MaterialFoundry/MaterialPlane/docs/index.md

# Material Plane Documentation

Welcome to the Material Plane documentation.

Click the links below or at the top of the page to navigate the documentation:

* [Production Hardware](Production/gettingStarted.md)
* [DIY Hardware](DIY/gettingStarted.md)
* [Touch](Touch/gettingStarted.md)
* [Display Considerations](DisplayConsiderations/type.md)
* [Hardware Comparison](hardwareComparison.md)
* [FAQ](faq.md)

## Introduction
Material Plane is a <a href="https://foundryvtt.com/">Foundry VTT</a> module that allows physical minis to be tracked by Foundry when using a horizontally mounted TV. This allows you to bring the joy of physical minis into Foundry.<br>
<br>
There are currently 2 ways to track minis:<br>

### Material Plane sensor
The system consists of an IR sensor, and IR enabled mini bases. These bases contain IR LEDs that are tracked by the sensor. The sensor then relays this information to foundry over WiFi, where the information is interpreted as token movement.<br>
You can use any TV, monitor or projector for this.<br>
There is a pre-assembled and advanced version of the hardware for sale on the [Material Foundry webshop](https://www.materialfoundry.nl/), or it is possible to build DIY hardware.

### Touch Screen
There is currently experimental support for touch screen devices. Either capacitive touch screens or normal TVs with an IR touch frame can work.<br>
<br>
Please take a look at [this](hardwareComparison.md) page for a comparison between the Material Plane sensor and touch screen.<br>

## Trailer
<a href="https://www.youtube.com/watch?v=VVTjNrCfUwM">
trailer
</a>

## Important Links

* [Issues/Feature requests](https://github.com/MaterialFoundry/MaterialPlane/issues)
* [Main repository](https://github.com/materialfoundry/materialplane)
* [Foundry module](https://github.com/MaterialFoundry/MaterialPlane_Foundry) ([Releases](https://github.com/MaterialFoundry/MaterialPlane_Foundry/releases))
* [Sensor firmware](https://github.com/MaterialFoundry/MaterialPlane_Sensor) ([Releases](https://github.com/MaterialFoundry/MaterialPlane_Sensor/releases))
* [Base firmware](https://github.com/MaterialFoundry/MaterialPlane_Base) ([Releases](https://github.com/MaterialFoundry/MaterialPlane_Base/releases))
* [Pen firmware](https://github.com/MaterialFoundry/MaterialPlane_Pen) ([Releases](https://github.com/MaterialFoundry/MaterialPlane_Pen/releases))
* [Material Companion](https://github.com/MaterialFoundry/MaterialCompanion) ([Releases](https://github.com/MaterialFoundry/MaterialCompanion/releases))
* [Arduino core](https://github.com/MaterialFoundry/MaterialFoundry_Arduino) ([Releases](https://github.com/MaterialFoundry/MaterialFoundry_Arduino/releases))
* [3D models](https://github.com/MaterialFoundry/MaterialPlane_Models)
* [Discord server](https://discord.gg/3hd4G6TkmA)
* [Patreon](https://www.patreon.com/materialfoundry)

## Software Versions & Module Incompatibilities
<b>Foundry VTT:</b> v10 & v11<br>
<b>Module Incompatibilities:</b> When moving tokens, Foundry's click and drag system is bypassed. So modules that depend on that functionality might not work.

## Feedback
If you have any suggestions or bugs to report, feel free to contact me on Discord (Cris#6864), or send me an email: info@materialfoundry.nl.

## Credits
<b>Author:</b> Cristian Deenen (Cris#6864 on Discord)<br>
<br>
Please consider supporting me on <a href="https://www.patreon.com/materialfoundry">Patreon</a>, and feel free to join the Material Foundry <a href="https://discord.gg/3hd4G6TkmA">Discord</a> server.
