MaterialFoundry/MaterialPlane/include/diyDisclaimer.md

<div class="warning" style='background-color:#ab4a00; border-radius: 4px; padding:0.7em; color:black; text-align: center;'>
<span>
<p style='margin-top:1em; text-align:center'>
<b>Disclaimer</b></p>
<p style='margin-left:1em;'>
For the DIY hardware you will, as the name suggest, have do it yourself. This includes sourcing parts, basic soldering, and 3D printing. You will be responsible for all troubleshooting.<br><br>
It is your own responsibility to properly build and use the hardware.
Material Foundry cannot be held responsible for any damage, either directly or indirectly caused by Material Foundry or any associated hardware, software or service.
This includes damage caused by incorrect documentation, bugs in the software or firmware, or wrong advise.<br>
<br>
If you are uncomfortable with this, consider buying the <a href="https://www.materialfoundry.nl/" style='color: #000f99'>pre-build production hardware</a>.
</p>
</div>
