MaterialFoundry/MaterialPlane/include/foundryConfig-downloads.md

## Downloads

In the 'Downloads' tab you can download the various firmwares for the Material Plane hardware, and Material Companion.

For each component, you can see the current version, the minimum version (that works with this version of the module), and the latest version.

Select the desired 'variant' (if applicable) and press the 'Download' button to download the file.
