MaterialFoundry/MaterialPlane/docs/DIY/Foundry/foundryConfig.md

{%set variant = 'diy' %}

{% include 'foundryConfig-general.md' %}

{% include 'foundryConfig-sensor.md' %}

{% include 'foundryConfig-downloads.md' %}
