MaterialFoundry/MaterialPlane/docs/DIY/SensorConfiguration/webserver.md

{%set variant = 'diy' %}

{% include 'sensorWebserver.md' %}
