MaterialFoundry/MaterialPlane/docs/DIY/SensorPositioning/sensorOrientation.md

{% set variant = 'diy' %}

{% include 'sensorOrientation.md' %}
