MaterialFoundry/MaterialPlane/docs/DIY/Updating/sensorUpdating.md

{%set variant = 'diy' %}

{% include 'sensorUpdating.md' %}
