MaterialFoundry/MaterialPlane/docs/DIY/SensorConfiguration/sensorSettings.md

{%set variant = 'production' %}

{% include 'sensorSettings.md' %}
