MaterialFoundry/MaterialPlane/docs/Production/Updating/sensorUpdating.md

{%set variant = 'production' %}

{% include 'sensorUpdating.md' %}
