MaterialFoundry/MaterialPlane/docs/Production/SensorPositioning/sensorDistance.md

{% set variant = 'production' %}
{% set lensLink = '../SensorConfiguration/sensorLens.md' %}

{% include 'requirements-displaySensorDistance.md' %}
