MaterialFoundry/MaterialPlane/docs/Production/SensorPositioning/sensorOrientation.md

{% set variant = 'production' %}
{% set lensLink = '../SensorConfiguration/sensorLens.md' %}

{% include 'sensorOrientation.md' %}
