MaterialFoundry/MaterialPlane/docs/img/foundry/.thumb/Foundry_Cal_Multi_Progress.png.jpg

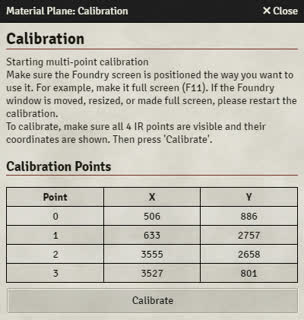
docs/img/foundry/.thumb/Foundry_Cal_Multi_Progress.png.jpg
