MaterialFoundry/MaterialPlane/docs/img/foundry/.thumb/Foundry_Module_Connection.png.jpg

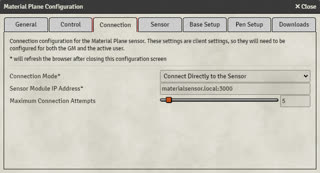
docs/img/foundry/.thumb/Foundry_Module_Connection.png.jpg
