MaterialFoundry/MaterialPlane/docs/img/foundry/.thumb/Foundry_Module_Control.png.jpg

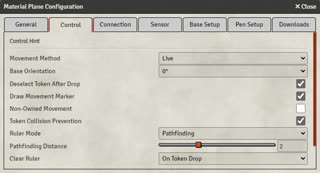
docs/img/foundry/.thumb/Foundry_Module_Control.png.jpg
