MaterialFoundry/MaterialPlane/docs/img/foundry/.thumb/Foundry_Module_Download.png.jpg

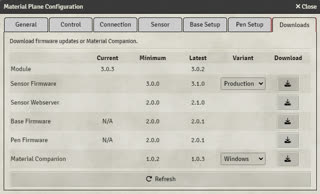
docs/img/foundry/.thumb/Foundry_Module_Download.png.jpg
