MaterialFoundry/MaterialPlane/docs/img/foundry/.thumb/Foundry_Module_Enable.png.jpg

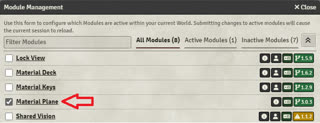
docs/img/foundry/.thumb/Foundry_Module_Enable.png.jpg
