MaterialFoundry/MaterialPlane/docs/img/foundry/.thumb/Foundry_Module_General_Touch.png.jpg

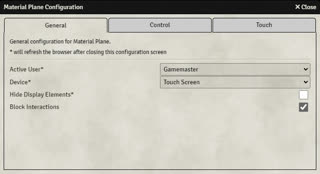
docs/img/foundry/.thumb/Foundry_Module_General_Touch.png.jpg
