MaterialFoundry/MaterialPlane/docs/img/foundry/.thumb/Foundry_Module_Pen.png.jpg

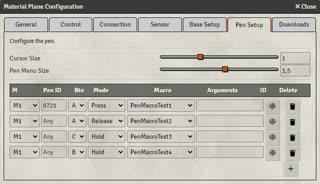
docs/img/foundry/.thumb/Foundry_Module_Pen.png.jpg
