MaterialFoundry/MaterialPlane/docs/img/foundry/.thumb/Foundry_Module_Update_All.png.jpg

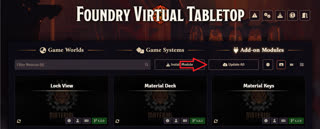
docs/img/foundry/.thumb/Foundry_Module_Update_All.png.jpg
