MaterialFoundry/MaterialPlane/docs/img/foundry/.thumb/Foundry_Module_Update_Single.png.jpg

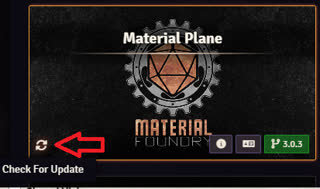
docs/img/foundry/.thumb/Foundry_Module_Update_Single.png.jpg
