MaterialFoundry/MaterialPlane/docs/img/foundry/Foundry_Cal_Single_Progress.png

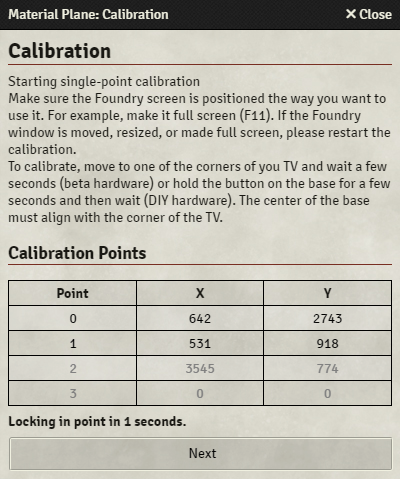
docs/img/foundry/Foundry_Cal_Single_Progress.png
