MaterialFoundry/MaterialPlane/docs/img/foundry/Foundry_Module_Config_Btn.png

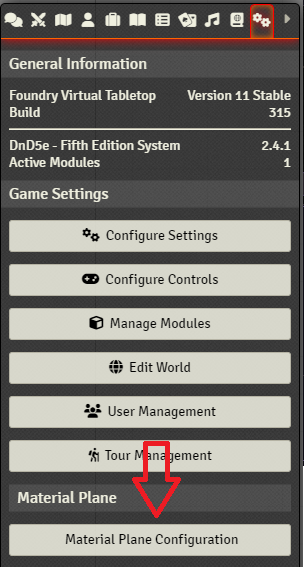
docs/img/foundry/Foundry_Module_Config_Btn.png
