MaterialFoundry/MaterialPlane/docs/img/foundry/Foundry_Module_Download.png

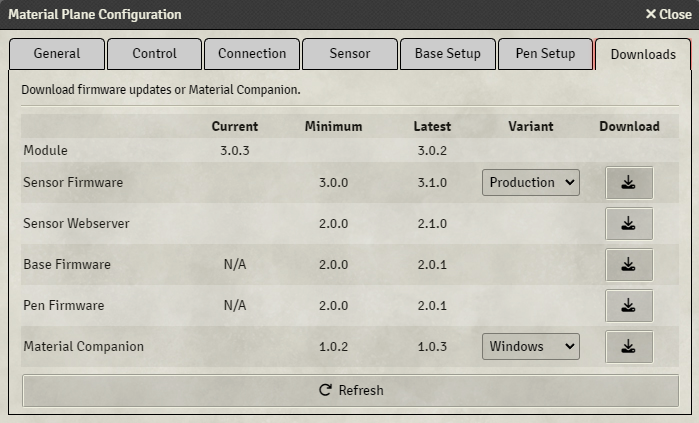
docs/img/foundry/Foundry_Module_Download.png
