MaterialFoundry/MaterialPlane/docs/img/foundry/Foundry_Module_General.png

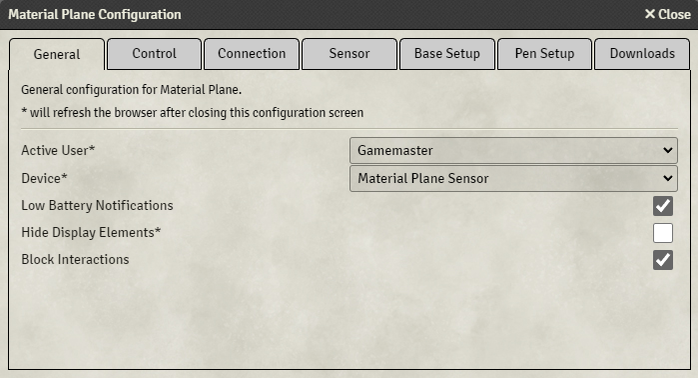
docs/img/foundry/Foundry_Module_General.png
