MaterialFoundry/MaterialPlane/docs/img/hardware/DIY/.thumb/BaseFab.jpg.jpg

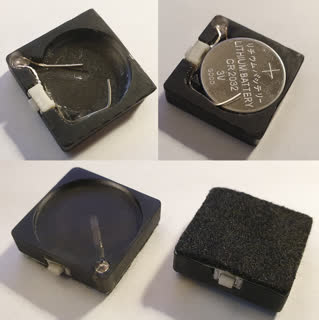
docs/img/hardware/DIY/.thumb/BaseFab.jpg.jpg
