MaterialFoundry/MaterialPlane/docs/img/hardware/DIY/.thumb/DFRobot.jpg.jpg

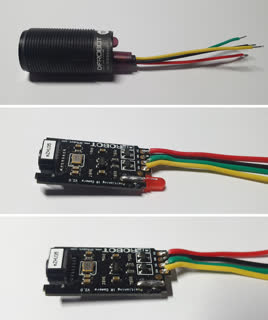
docs/img/hardware/DIY/.thumb/DFRobot.jpg.jpg
