MaterialFoundry/MaterialPlane/docs/img/hardware/DIY/.thumb/Enclosure.jpg.jpg

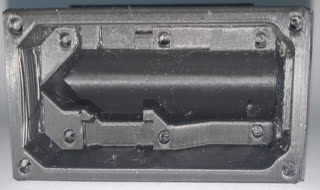
docs/img/hardware/DIY/.thumb/Enclosure.jpg.jpg
