MaterialFoundry/MaterialPlane/docs/img/hardware/DIY/.thumb/GndLead.jpg.jpg

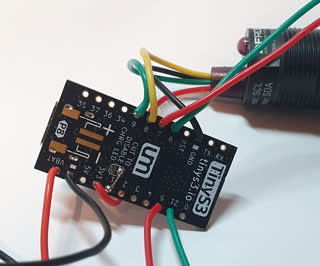
docs/img/hardware/DIY/.thumb/GndLead.jpg.jpg
