MaterialFoundry/MaterialPlane/docs/img/hardware/DIY/.thumb/MiniWithBase.jpg.jpg

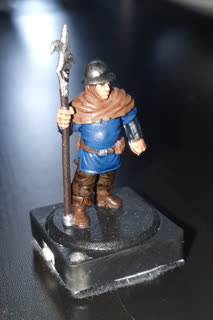
docs/img/hardware/DIY/.thumb/MiniWithBase.jpg.jpg
