MaterialFoundry/MaterialPlane/docs/img/hardware/DIY/.thumb/Sensor.jpg.jpg

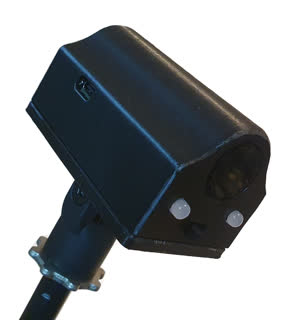
docs/img/hardware/DIY/.thumb/Sensor.jpg.jpg
