MaterialFoundry/MaterialPlane/docs/img/hardware/DIY/.thumb/Switch.jpg.jpg

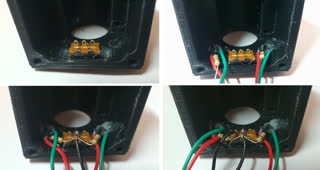
docs/img/hardware/DIY/.thumb/Switch.jpg.jpg
