MaterialFoundry/MaterialPlane/docs/img/hardware/DIY/.thumb/TinyPicoUsbDetect.jpg.jpg

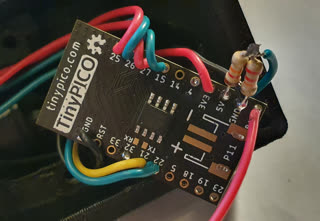
docs/img/hardware/DIY/.thumb/TinyPicoUsbDetect.jpg.jpg
