MaterialFoundry/MaterialPlane/docs/img/hardware/DIY/.thumb/TinyS3UsbDetect.jpg.jpg

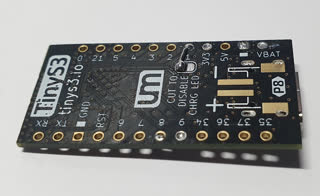
docs/img/hardware/DIY/.thumb/TinyS3UsbDetect.jpg.jpg
