MaterialFoundry/MaterialPlane/docs/img/hardware/production/.thumb/Base_Adapter_Prod.png.jpg

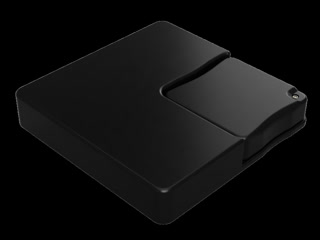
docs/img/hardware/production/.thumb/Base_Adapter_Prod.png.jpg
