MaterialFoundry/MaterialPlane/docs/img/hardware/production/.thumb/Base_Prod.png.jpg

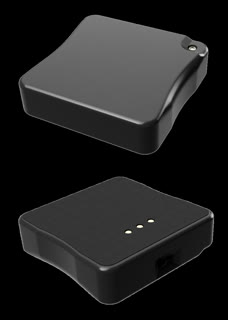
docs/img/hardware/production/.thumb/Base_Prod.png.jpg
