MaterialFoundry/MaterialPlane/docs/img/hardware/production/.thumb/Dock_Charging.png.jpg

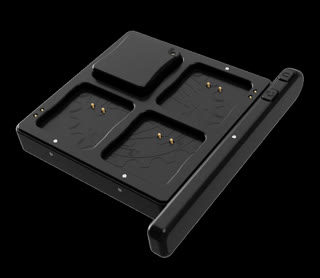
docs/img/hardware/production/.thumb/Dock_Charging.png.jpg
