MaterialFoundry/MaterialPlane/docs/img/hardware/production/.thumb/Dock_Prod.png.jpg

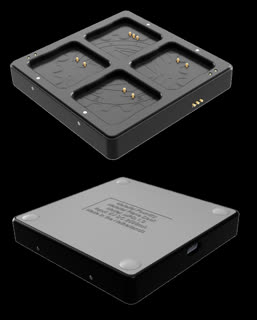
docs/img/hardware/production/.thumb/Dock_Prod.png.jpg
