MaterialFoundry/MaterialPlane/docs/img/hardware/production/.thumb/Expansions_Prod.png.jpg

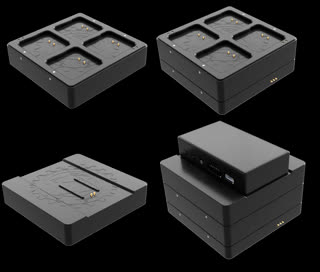
docs/img/hardware/production/.thumb/Expansions_Prod.png.jpg
