MaterialFoundry/MaterialPlane/docs/img/hardware/production/.thumb/Mini_Holding.png.jpg

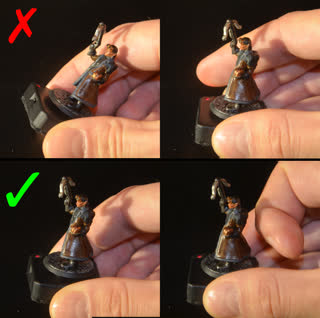
docs/img/hardware/production/.thumb/Mini_Holding.png.jpg
