MaterialFoundry/MaterialPlane/docs/img/hardware/production/.thumb/Mini_Mounting.png.jpg

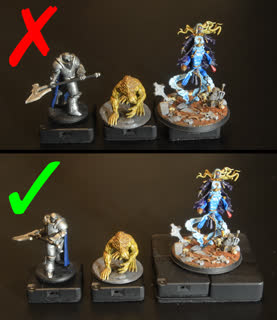
docs/img/hardware/production/.thumb/Mini_Mounting.png.jpg
