MaterialFoundry/MaterialPlane/docs/img/hardware/production/.thumb/Pen_Holding.png.jpg

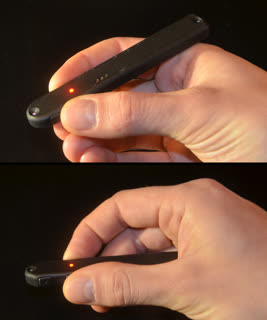
docs/img/hardware/production/.thumb/Pen_Holding.png.jpg
