MaterialFoundry/MaterialPlane/docs/img/hardware/production/.thumb/Pen_Prod.png.jpg

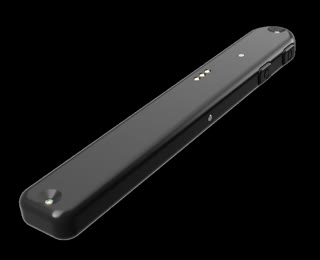
docs/img/hardware/production/.thumb/Pen_Prod.png.jpg
