MaterialFoundry/MaterialPlane/docs/img/hardware/production/.thumb/Sensor_Lens_Removal.png.jpg

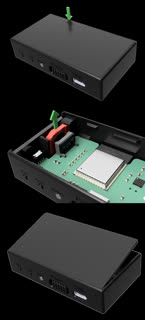
docs/img/hardware/production/.thumb/Sensor_Lens_Removal.png.jpg
