MaterialFoundry/MaterialPlane/docs/img/hardware/production/.thumb/Sensor_Mount.png.jpg

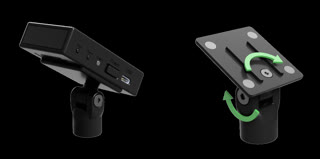
docs/img/hardware/production/.thumb/Sensor_Mount.png.jpg
