MaterialFoundry/MaterialPlane/docs/img/hardware/production/.thumb/Sensor_Mount_Ceiling.png.jpg

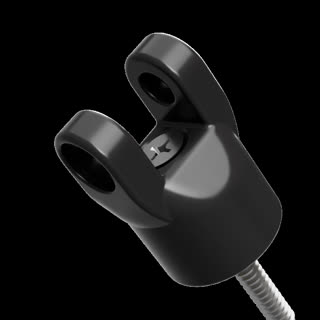
docs/img/hardware/production/.thumb/Sensor_Mount_Ceiling.png.jpg
