MaterialFoundry/MaterialPlane/docs/img/hardware/production/.thumb/Sensor_Prod.png.jpg

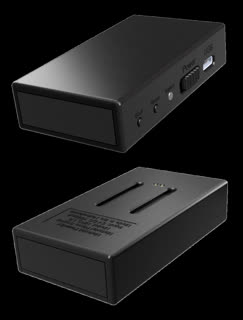
docs/img/hardware/production/.thumb/Sensor_Prod.png.jpg
