MaterialFoundry/MaterialPlane/docs/img/hardware/production/Sensor_Lens_Removal.png

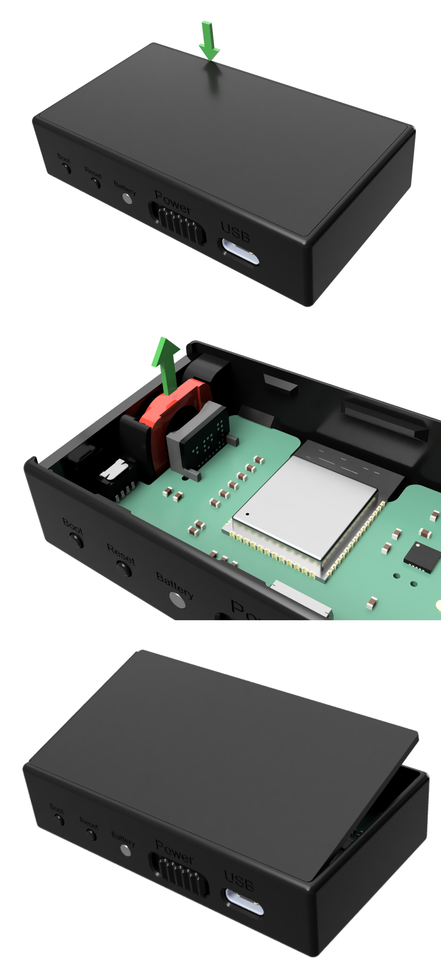
docs/img/hardware/production/Sensor_Lens_Removal.png
