MaterialFoundry/MaterialPlane/docs/img/misc/.thumb/Arduino_Boards.png.jpg

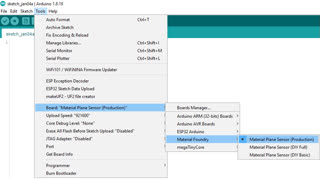
docs/img/misc/.thumb/Arduino_Boards.png.jpg
