MaterialFoundry/MaterialPlane/docs/img/misc/.thumb/Arduino_Port.png.jpg

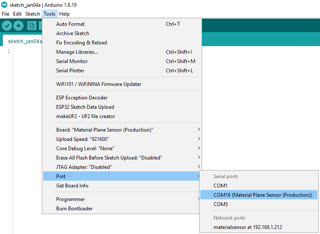
docs/img/misc/.thumb/Arduino_Port.png.jpg
