MaterialFoundry/MaterialPlane/docs/img/misc/.thumb/Arduino_Spiffs.png.jpg

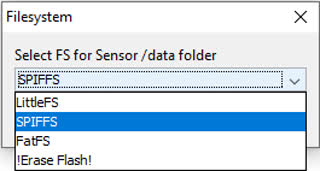
docs/img/misc/.thumb/Arduino_Spiffs.png.jpg
