MaterialFoundry/MaterialPlane/docs/img/misc/.thumb/Arduino_Upload.png.jpg

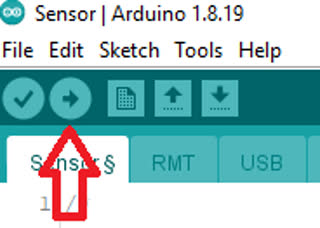
docs/img/misc/.thumb/Arduino_Upload.png.jpg
