MaterialFoundry/MaterialPlane/docs/img/misc/.thumb/Display_Protection.png.jpg

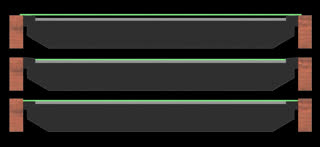
docs/img/misc/.thumb/Display_Protection.png.jpg
