MaterialFoundry/MaterialPlane/docs/img/misc/.thumb/Sensor_Placement_GM_Short.png.jpg

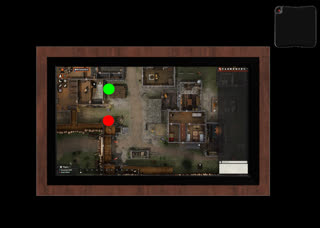
docs/img/misc/.thumb/Sensor_Placement_GM_Short.png.jpg
