MaterialFoundry/MaterialPlane/docs/img/misc/.thumb/SensorPlacement.png.jpg

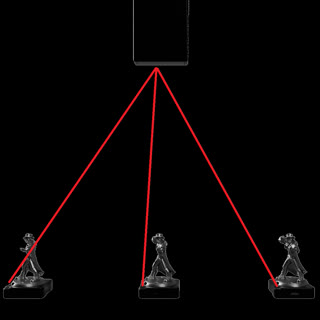
docs/img/misc/.thumb/SensorPlacement.png.jpg
