MaterialFoundry/MaterialPlane/docs/img/misc/.thumb/Serial_Scan_Wifi.png.jpg

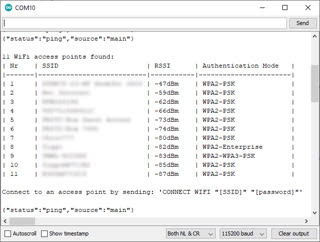
docs/img/misc/.thumb/Serial_Scan_Wifi.png.jpg
