MaterialFoundry/MaterialPlane/docs/img/misc/Arduino_Boards_Manager.png

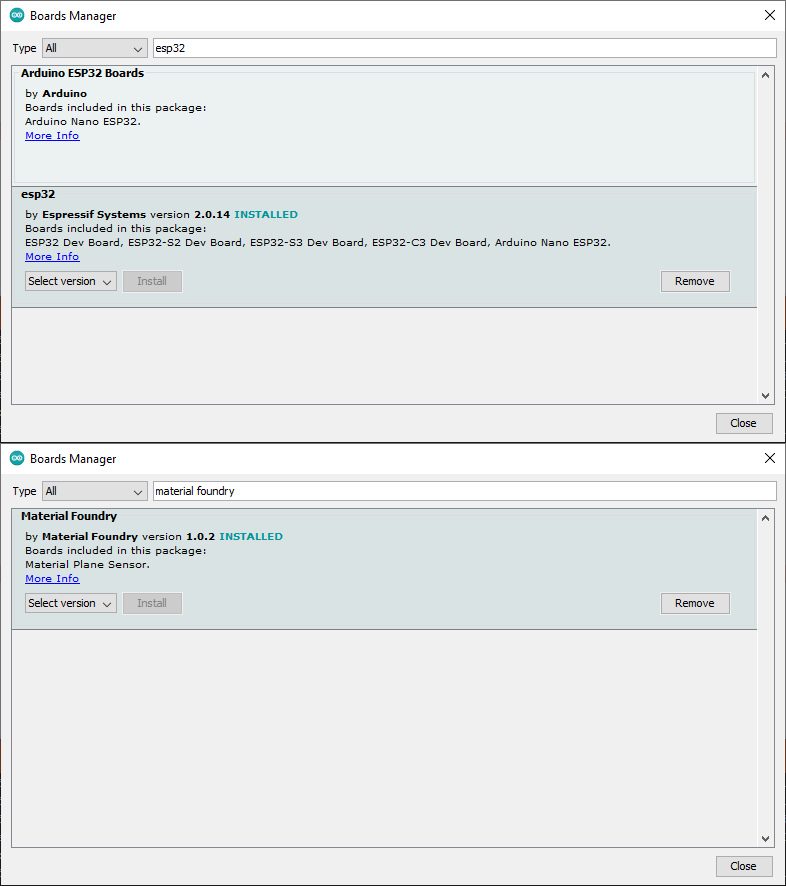
docs/img/misc/Arduino_Boards_Manager.png
