MaterialFoundry/MaterialPlane/docs/img/webserver/.thumb/Webserver_Console.png.jpg

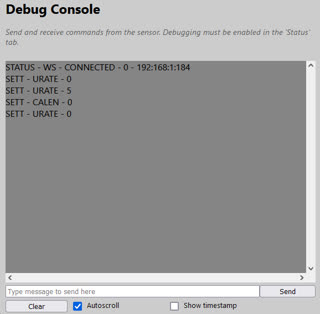
docs/img/webserver/.thumb/Webserver_Console.png.jpg
