MaterialFoundry/MaterialPlane/docs/img/webserver/.thumb/Webserver_Coordinates.png.jpg

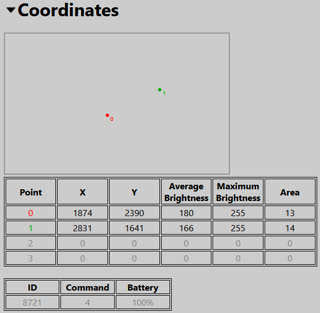
docs/img/webserver/.thumb/Webserver_Coordinates.png.jpg
