MaterialFoundry/MaterialPlane/docs/img/webserver/.thumb/Webserver_Coordinates_DIY.png.jpg

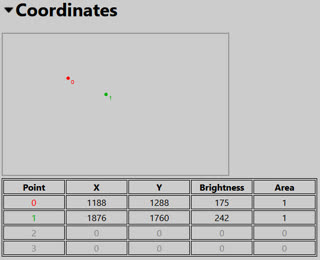
docs/img/webserver/.thumb/Webserver_Coordinates_DIY.png.jpg
