MaterialFoundry/MaterialPlane/docs/img/webserver/.thumb/Webserver_Reset.png.jpg

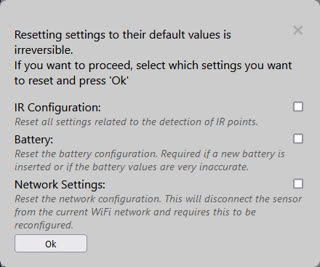
docs/img/webserver/.thumb/Webserver_Reset.png.jpg
