MaterialFoundry/MaterialPlane/docs/img/webserver/.thumb/Webserver_Update.png.jpg

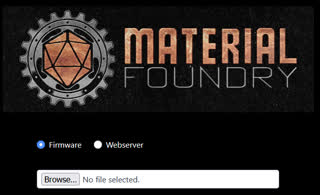
docs/img/webserver/.thumb/Webserver_Update.png.jpg
