MaterialFoundry/MaterialPlane/docs/img/webserver/Webserver_Battery_DIY.png

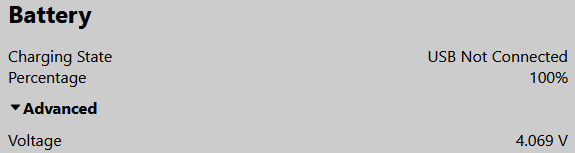
docs/img/webserver/Webserver_Battery_DIY.png
