MaterialFoundry/MaterialPlane/docs/img/webserver/Webserver_Status.png

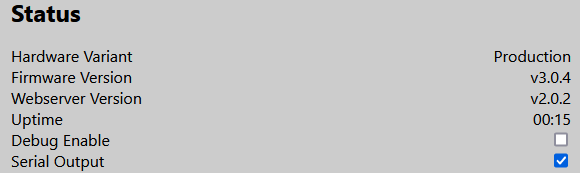
docs/img/webserver/Webserver_Status.png
