MaterialFoundry/MaterialPlane/docs/img/webserver/Webserver_Status_Tab.png

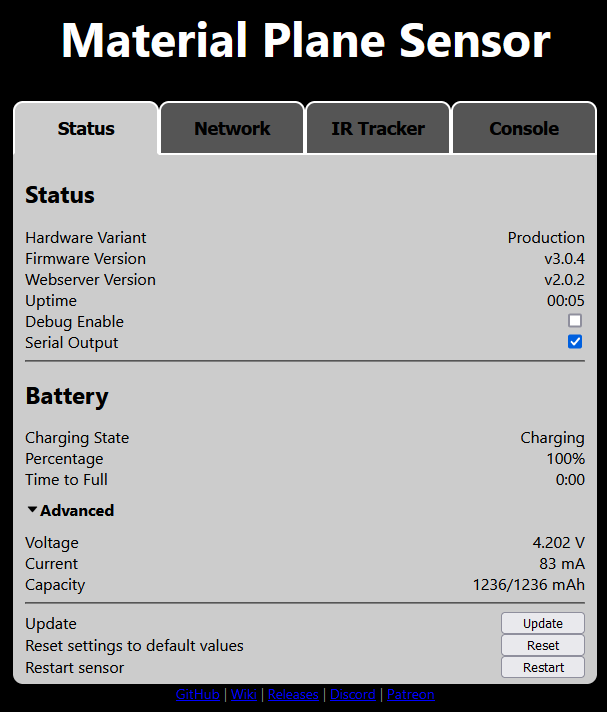
docs/img/webserver/Webserver_Status_Tab.png
