MaterialFoundry/MaterialPlane/Img/Beta Hardware/20210420_232709.jpg

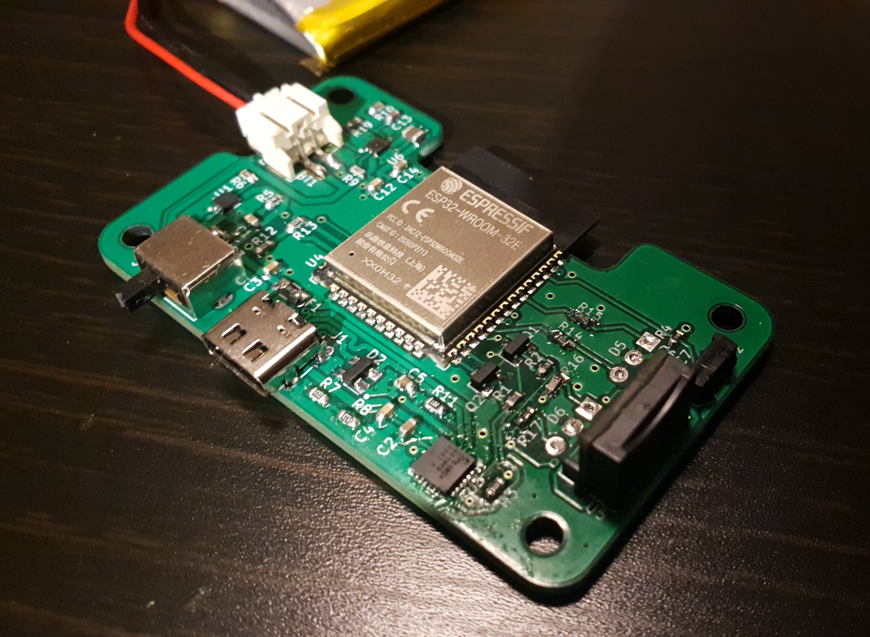
Img/Beta Hardware/20210420_232709.jpg
