MaterialFoundry/MaterialPlane/Img/Beta Hardware/.thumb/Base.jpg.jpg

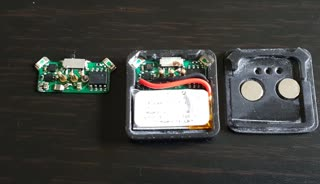
Img/Beta Hardware/.thumb/Base.jpg.jpg
