MaterialFoundry/MaterialPlane/Img/Beta Hardware/.thumb/MP_Base.jpg.jpg

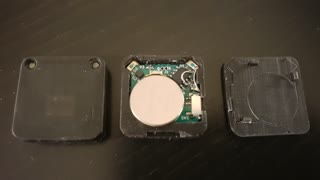
Img/Beta Hardware/.thumb/MP_Base.jpg.jpg
