MaterialFoundry/MaterialPlane/Img/Beta Hardware/.thumb/MP_Dock_ConceptArt.png.jpg

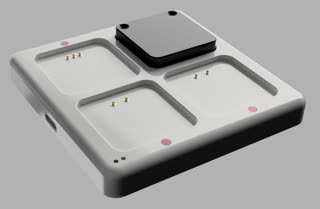
Img/Beta Hardware/.thumb/MP_Dock_ConceptArt.png.jpg
