MaterialFoundry/MaterialPlane/Img/Beta Hardware/.thumb/MP_PCBs.jpg.jpg

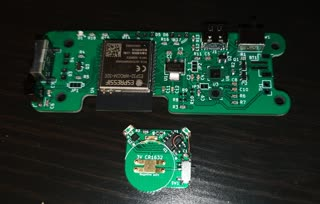
Img/Beta Hardware/.thumb/MP_PCBs.jpg.jpg
