MaterialFoundry/MaterialPlane/Img/Beta Hardware/.thumb/SensorBaseAndDock.jpg.jpg

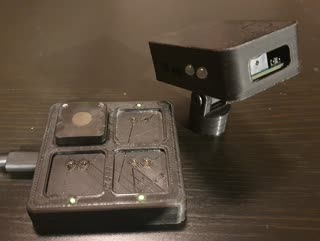
Img/Beta Hardware/.thumb/SensorBaseAndDock.jpg.jpg
