MaterialFoundry/MaterialPlane/Img/DIY Hardware/.thumb/BaseBottom.jpg.jpg

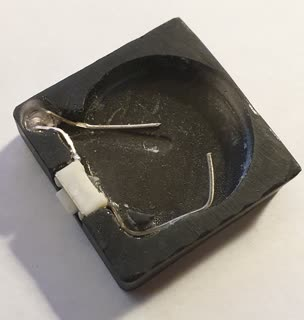
Img/DIY Hardware/.thumb/BaseBottom.jpg.jpg
