MaterialFoundry/MaterialPlane/Img/DIY Hardware/.thumb/BaseBottomBattery.jpg.jpg

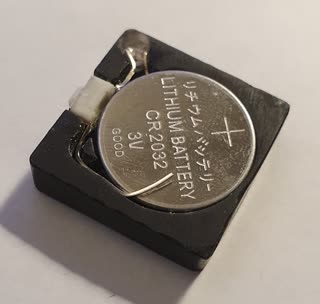
Img/DIY Hardware/.thumb/BaseBottomBattery.jpg.jpg
