MaterialFoundry/MaterialPlane/Img/DIY Hardware/.thumb/Bases.jpg.jpg

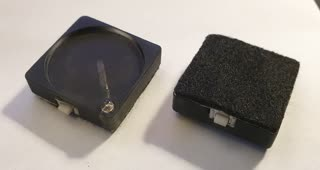
Img/DIY Hardware/.thumb/Bases.jpg.jpg
