MaterialFoundry/MaterialPlane/Img/DIY Hardware/.thumb/Battery.jpg.jpg

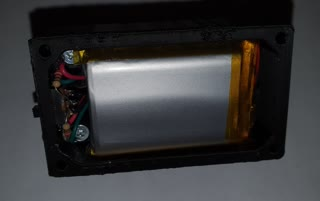
Img/DIY Hardware/.thumb/Battery.jpg.jpg
