MaterialFoundry/MaterialPlane/Img/DIY Hardware/.thumb/Brackets.jpg.jpg

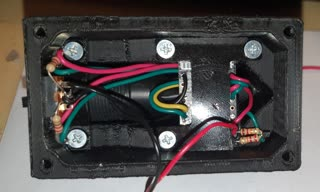
Img/DIY Hardware/.thumb/Brackets.jpg.jpg
