MaterialFoundry/MaterialPlane/Img/DIY Hardware/.thumb/FullSensor.jpg.jpg

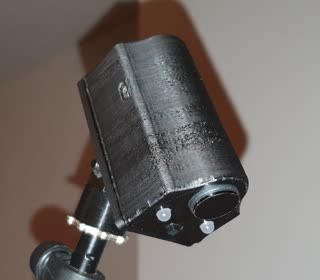
Img/DIY Hardware/.thumb/FullSensor.jpg.jpg
