MaterialFoundry/MaterialPlane/Img/DIY Hardware/.thumb/LEDsNextToSwitch.jpg.jpg

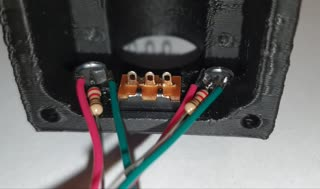
Img/DIY Hardware/.thumb/LEDsNextToSwitch.jpg.jpg
