MaterialFoundry/MaterialPlane/Img/DIY Hardware/.thumb/Lid.jpg.jpg

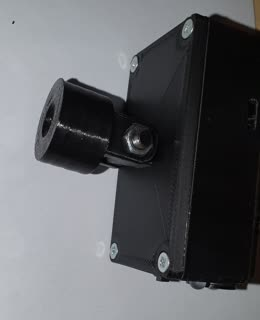
Img/DIY Hardware/.thumb/Lid.jpg.jpg
