MaterialFoundry/MaterialPlane/Img/DIY Hardware/.thumb/RemoveLED1.jpg.jpg

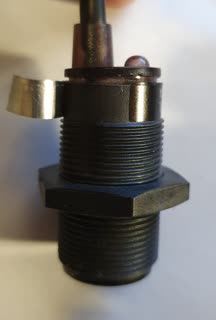
Img/DIY Hardware/.thumb/RemoveLED1.jpg.jpg
