MaterialFoundry/MaterialPlane/Img/DIY Hardware/.thumb/RemoveLED2.jpg.jpg

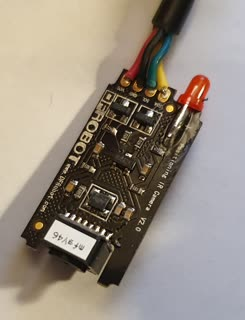
Img/DIY Hardware/.thumb/RemoveLED2.jpg.jpg
