MaterialFoundry/MaterialPlane/Img/DIY Hardware/.thumb/RemoveLED3.jpg.jpg

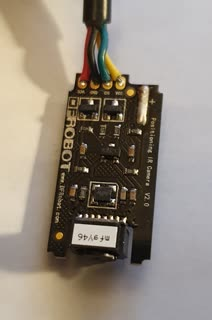
Img/DIY Hardware/.thumb/RemoveLED3.jpg.jpg
