MaterialFoundry/MaterialPlane/Img/DIY Hardware/.thumb/SensorCutWires.jpg.jpg

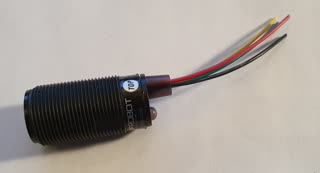
Img/DIY Hardware/.thumb/SensorCutWires.jpg.jpg
