MaterialFoundry/MaterialPlane/Img/DIY Hardware/.thumb/SensorMount.jpg.jpg

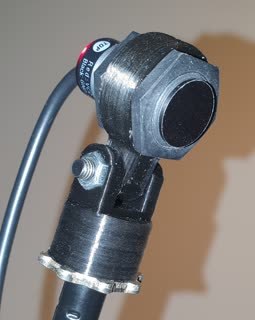
Img/DIY Hardware/.thumb/SensorMount.jpg.jpg
