MaterialFoundry/MaterialPlane/Img/DIY Hardware/.thumb/Switches2.jpg.jpg

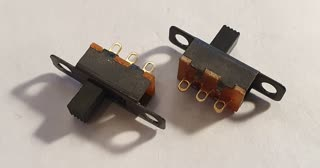
Img/DIY Hardware/.thumb/Switches2.jpg.jpg
