MaterialFoundry/MaterialPlane/Img/DIY Hardware/.thumb/Switches.jpg.jpg

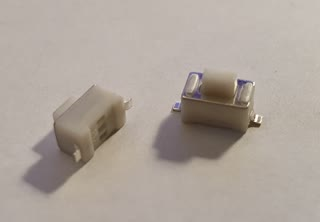
Img/DIY Hardware/.thumb/Switches.jpg.jpg
