MaterialFoundry/MaterialPlane/Img/DIY Hardware/.thumb/SwitchWired.jpg.jpg

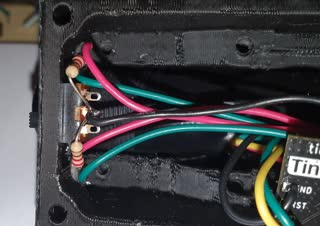
Img/DIY Hardware/.thumb/SwitchWired.jpg.jpg
