MaterialFoundry/MaterialPlane/Img/Module/.thumb/Config_Base.jpg.jpg

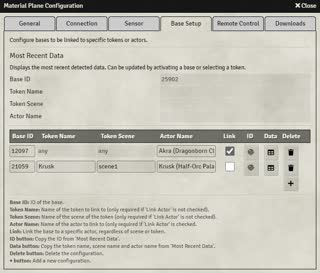
Img/Module/.thumb/Config_Base.jpg.jpg
