MaterialFoundry/MaterialPlane/Img/Module/.thumb/Config_Downloads.jpg.jpg

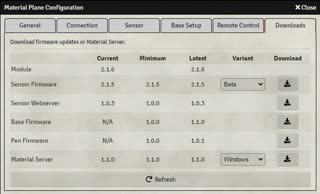
Img/Module/.thumb/Config_Downloads.jpg.jpg
