MaterialFoundry/MaterialPlane/Img/Module/.thumb/Config_General_Sensor.jpg.jpg

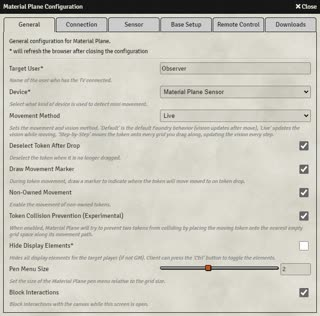
Img/Module/.thumb/Config_General_Sensor.jpg.jpg
