MaterialFoundry/MaterialPlane/Img/Module/.thumb/Config_Sensor.jpg.jpg

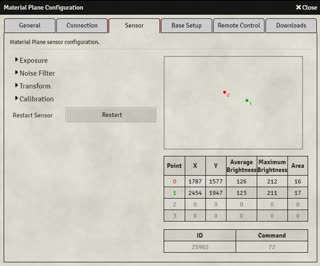
Img/Module/.thumb/Config_Sensor.jpg.jpg
