MaterialFoundry/MaterialPlane/Img/Module/.thumb/Config_Touch.jpg.jpg

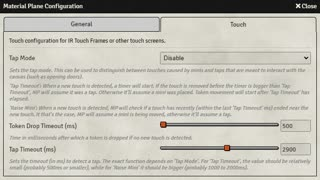
Img/Module/.thumb/Config_Touch.jpg.jpg
