MaterialFoundry/MaterialPlane/Img/Module/.thumb/MS_Status.jpg.jpg

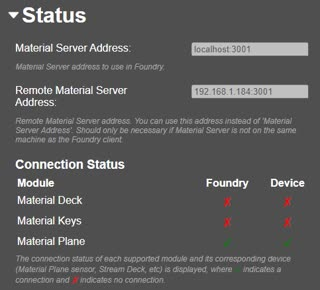
Img/Module/.thumb/MS_Status.jpg.jpg
