MaterialFoundry/MaterialPlane/Img/Module/Config_Base.jpg

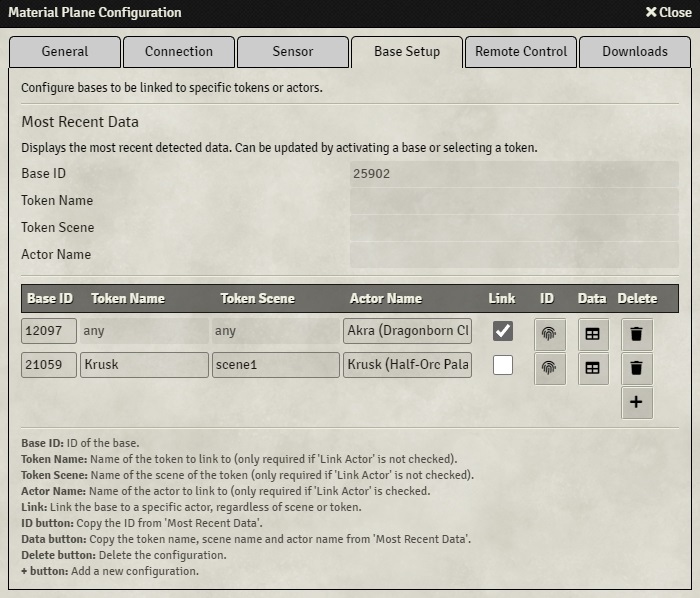
Img/Module/Config_Base.jpg
