MaterialFoundry/MaterialPlane/Img/Module/Config_Remote.jpg

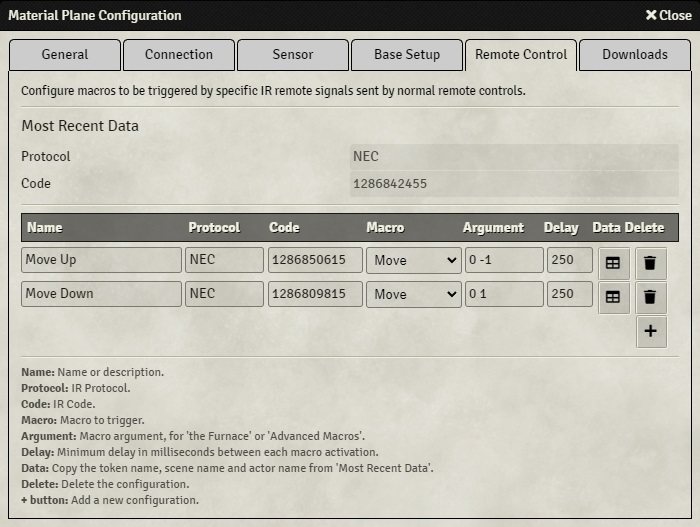
Img/Module/Config_Remote.jpg
