MaterialFoundry/MaterialPlane/Img/Module/Configuration/.thumb/General.png.jpg

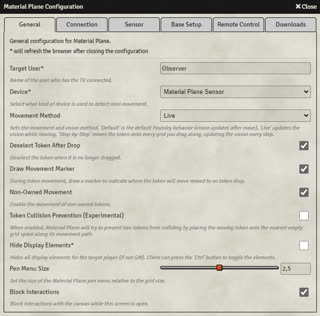
Img/Module/Configuration/.thumb/General.png.jpg
