MaterialFoundry/MaterialPlane/Img/Module/Configuration/.thumb/Remote.png.jpg

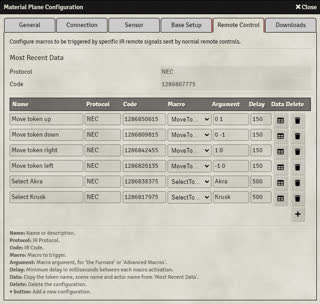
Img/Module/Configuration/.thumb/Remote.png.jpg
