MaterialFoundry/MaterialPlane/Img/Module/Configuration/Connection.png

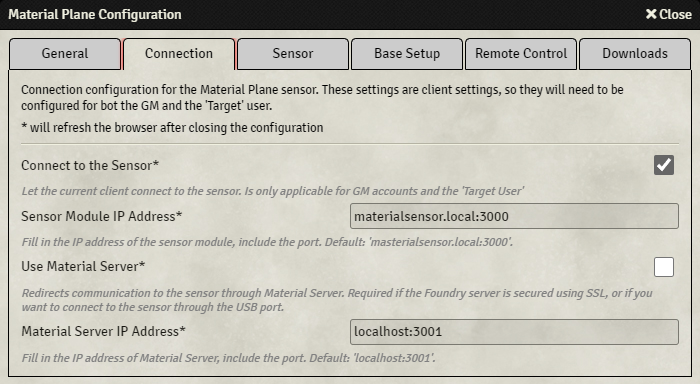
Img/Module/Configuration/Connection.png
