MaterialFoundry/MaterialPlane/Img/Module/Configuration/Touch.png

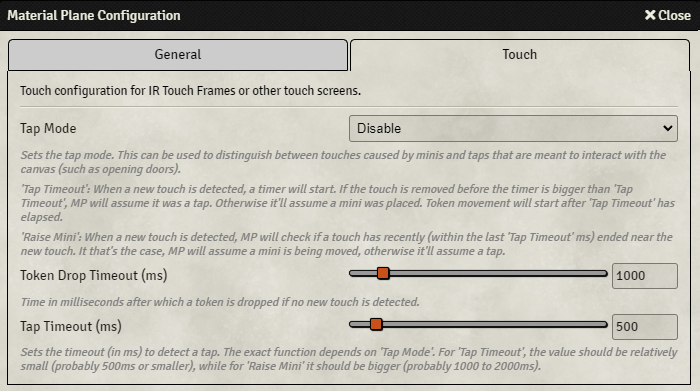
Img/Module/Configuration/Touch.png
