MaterialFoundry/MaterialPlane/Img/Module/ModuleSettings.jpg

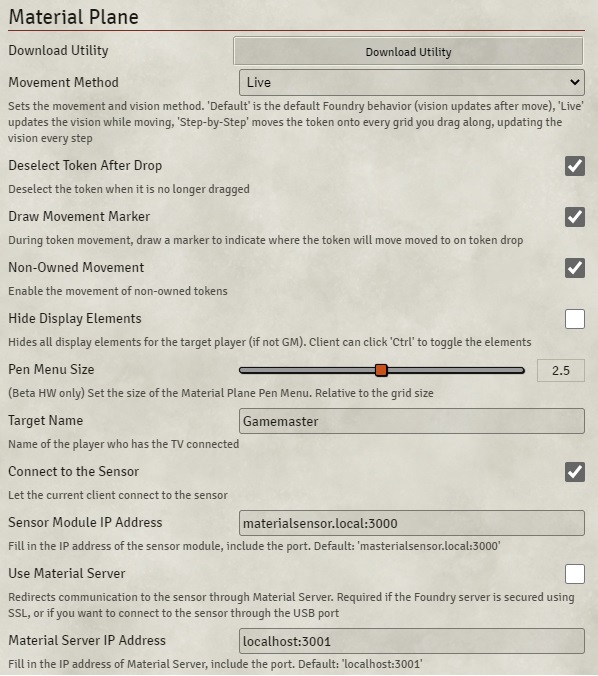
Img/Module/ModuleSettings.jpg
