MaterialFoundry/MaterialPlane/Img/Module/MS_MP.jpg

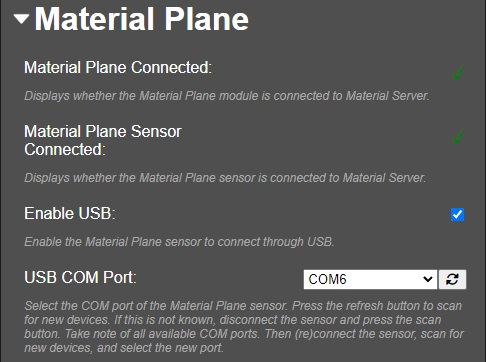
Img/Module/MS_MP.jpg
