MaterialFoundry/MaterialPlane/Img/Module/SidebarButtons.png

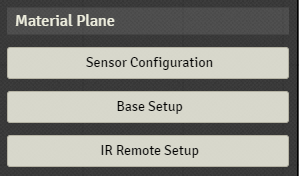
Img/Module/SidebarButtons.png
