MaterialFoundry/MaterialPlane/Img/Other/20250402_215641.jpg

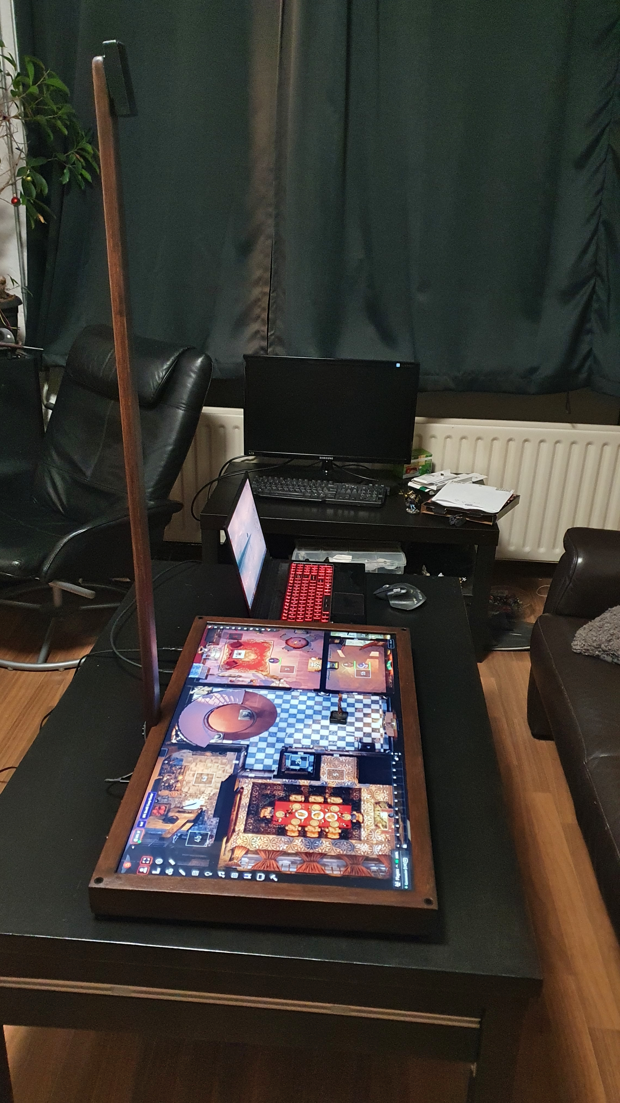
Img/Other/20250402_215641.jpg
