MaterialFoundry/MaterialPlane/Img/Other/.thumb/YoutubeVid.png.jpg

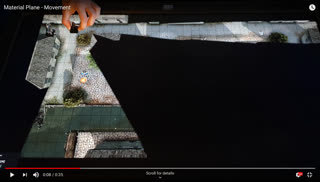
Img/Other/.thumb/YoutubeVid.png.jpg
