MaterialFoundry/MaterialPlane/Img/Other/SettingsVid.png

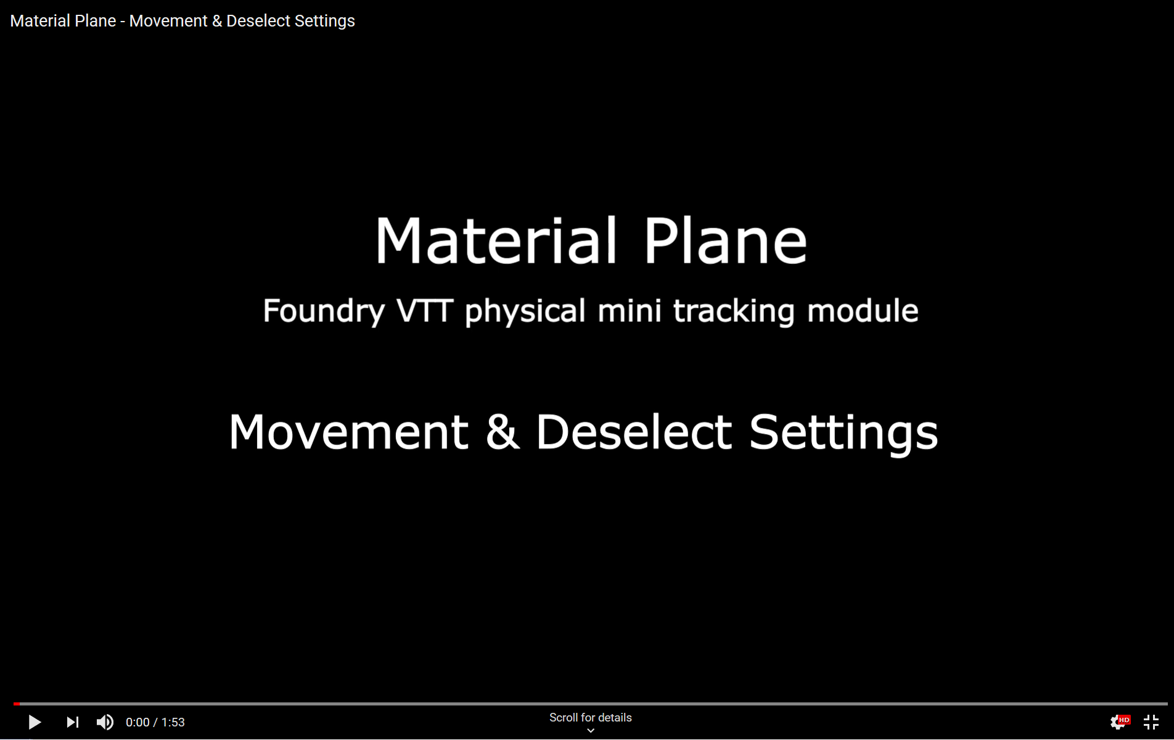
Img/Other/SettingsVid.png
