MaterialFoundry/MaterialPlane/Img/Sensor/Webserver/.thumb/EstablishingConnection.png.jpg

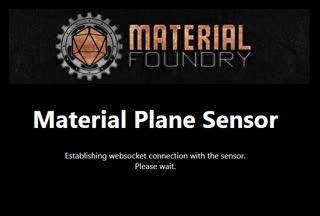
Img/Sensor/Webserver/.thumb/EstablishingConnection.png.jpg
