MaterialFoundry/MaterialPlane/Img/Sensor/Webserver/.thumb/IRtracker.jpg.jpg

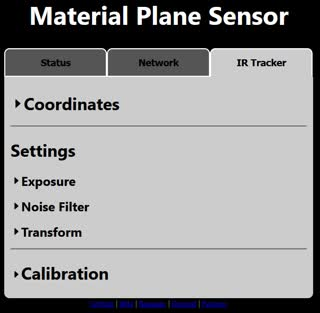
Img/Sensor/Webserver/.thumb/IRtracker.jpg.jpg
