MaterialFoundry/MaterialPlane/Img/Sensor/Webserver/.thumb/Status.png.jpg

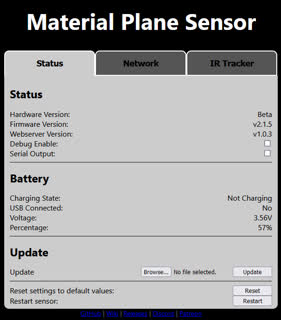
Img/Sensor/Webserver/.thumb/Status.png.jpg
