MaterialFoundry/MaterialPlane/docs/img/materialCompanion/.thumb/MaterialCompanion_Connect_Tab.png.jpg

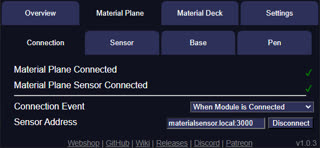
docs/img/materialCompanion/.thumb/MaterialCompanion_Connect_Tab.png.jpg
