MaterialFoundry/MaterialPlane/docs/img/materialCompanion/.thumb/MaterialCompanion_Sensor_USB_Update.png.jpg

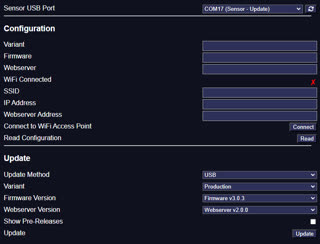
docs/img/materialCompanion/.thumb/MaterialCompanion_Sensor_USB_Update.png.jpg
