MaterialFoundry/MaterialPlane/docs/img/materialCompanion/MaterialCompanion_Sensor_WiFi_Update.png

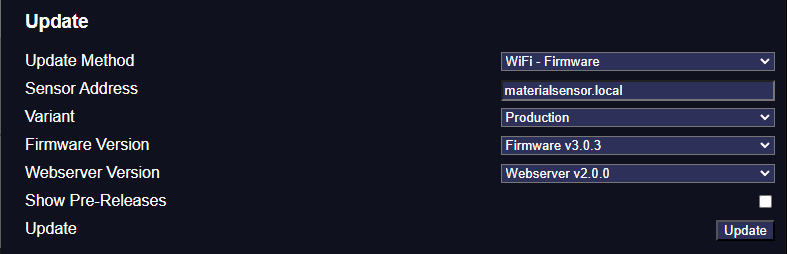
docs/img/materialCompanion/MaterialCompanion_Sensor_WiFi_Update.png
