MaterialFoundry/MaterialPlane/3D Models/Sensor Enclosure/Micstand Mount.step

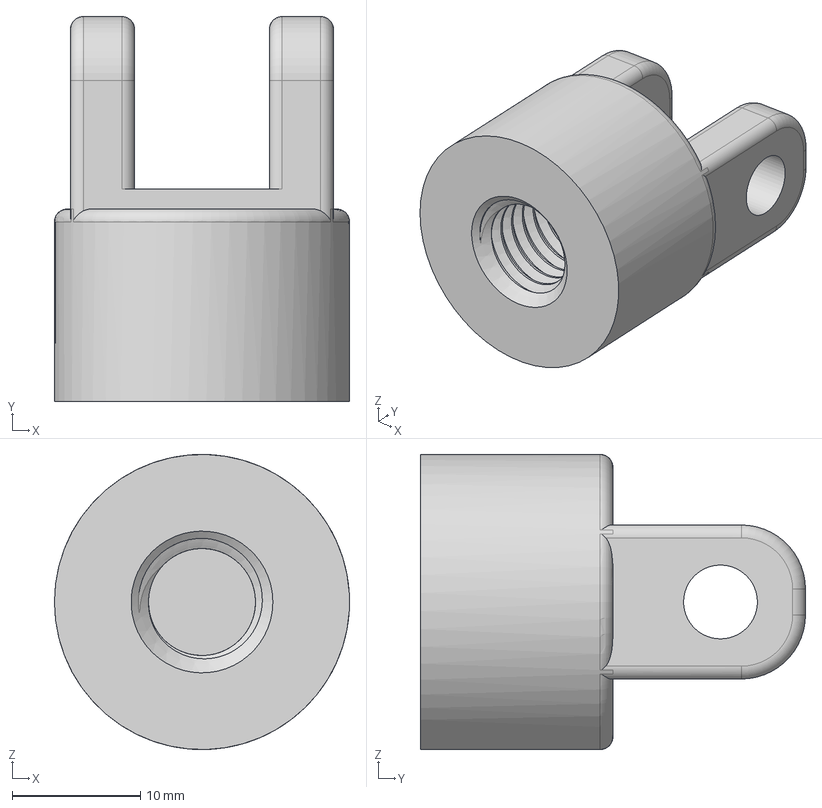
[picture p122: CAD file, 2020-09-23, last stored version]
3D Models/Sensor Enclosure/Micstand Mount.step
23.0 x 30.0 x 23.0 mm
