MaterialFoundry/MaterialPlane/docs/img/foundry/.thumb/Foundry_Module_Install.png.jpg

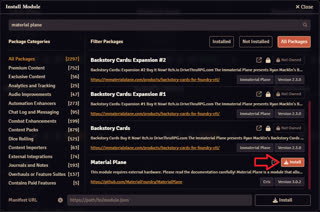
docs/img/foundry/.thumb/Foundry_Module_Install.png.jpg
