MaterialFoundry/MaterialPlane/docs/img/foundry/.thumb/Foundry_Module_Install_Btn.png.jpg

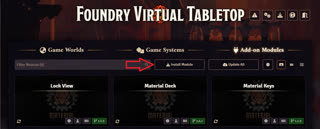
docs/img/foundry/.thumb/Foundry_Module_Install_Btn.png.jpg
