MaterialFoundry/MaterialPlane/docs/img/foundry/.thumb/Foundry_Module_Install_Manifest.png.jpg

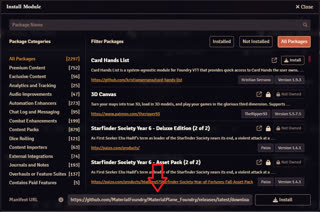
docs/img/foundry/.thumb/Foundry_Module_Install_Manifest.png.jpg
