MaterialFoundry/MaterialPlane/docs/img/foundry/.thumb/Foundry_Module_Uninstall.png.jpg

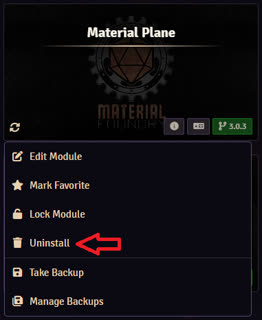
docs/img/foundry/.thumb/Foundry_Module_Uninstall.png.jpg
