MaterialFoundry/MaterialPlane/Img/Beta Hardware/Guide/.thumb/Base_Charge_Exp2.jpg.jpg

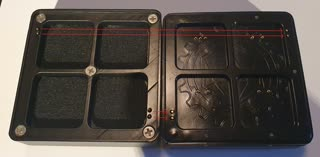
Img/Beta Hardware/Guide/.thumb/Base_Charge_Exp2.jpg.jpg
