MaterialFoundry/MaterialPlane/Img/Beta Hardware/Guide/.thumb/Base_Charge_Exp.jpg.jpg

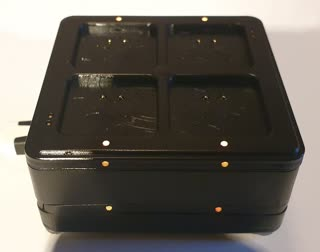
Img/Beta Hardware/Guide/.thumb/Base_Charge_Exp.jpg.jpg
