MaterialFoundry/MaterialPlane/Img/Beta Hardware/Guide/.thumb/Base_ChargeContacts.jpg.jpg

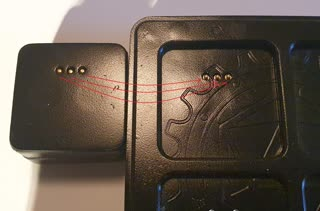
Img/Beta Hardware/Guide/.thumb/Base_ChargeContacts.jpg.jpg
