MaterialFoundry/MaterialPlane/Img/Beta Hardware/Guide/.thumb/Base_Charging.jpg.jpg

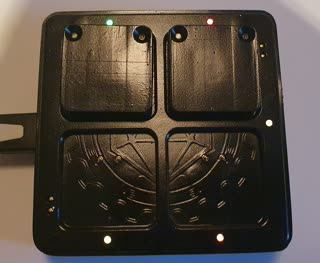
Img/Beta Hardware/Guide/.thumb/Base_Charging.jpg.jpg
