MaterialFoundry/MaterialPlane/Img/Beta Hardware/Guide/.thumb/Base_Front.jpg.jpg

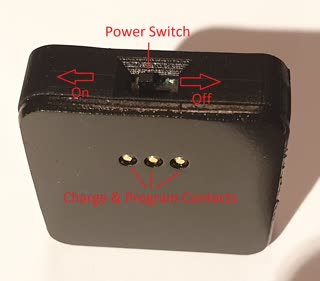
Img/Beta Hardware/Guide/.thumb/Base_Front.jpg.jpg
