MaterialFoundry/MaterialPlane/Img/Beta Hardware/Guide/.thumb/Base_Top.jpg.jpg

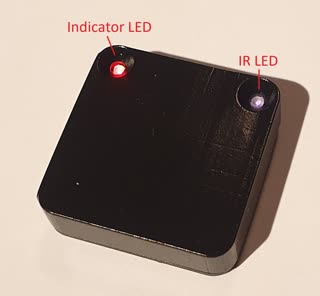
Img/Beta Hardware/Guide/.thumb/Base_Top.jpg.jpg
