MaterialFoundry/MaterialPlane/Img/Beta Hardware/Guide/.thumb/BaseGlue.jpg.jpg

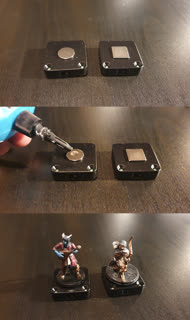
Img/Beta Hardware/Guide/.thumb/BaseGlue.jpg.jpg
