MaterialFoundry/MaterialPlane/Img/Beta Hardware/Guide/.thumb/BaseMount.jpg.jpg

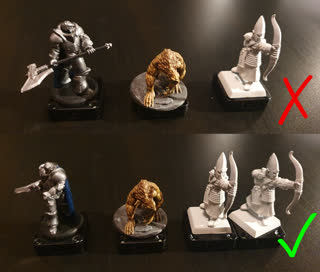
Img/Beta Hardware/Guide/.thumb/BaseMount.jpg.jpg
