MaterialFoundry/MaterialPlane/Img/Beta Hardware/Guide/.thumb/BaseMvmtObsc.jpg.jpg

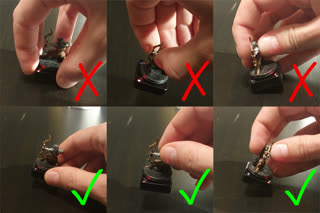
Img/Beta Hardware/Guide/.thumb/BaseMvmtObsc.jpg.jpg
