MaterialFoundry/MaterialPlane/Img/Beta Hardware/Guide/.thumb/Charging_Stack.jpg.jpg

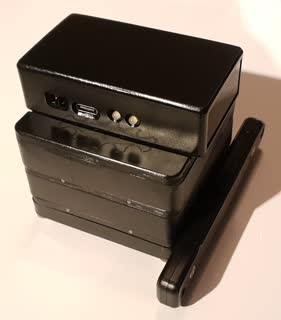
Img/Beta Hardware/Guide/.thumb/Charging_Stack.jpg.jpg
