MaterialFoundry/MaterialPlane/Img/Beta Hardware/Guide/.thumb/Dock_Top.jpg.jpg

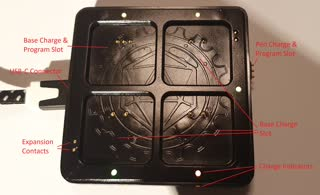
Img/Beta Hardware/Guide/.thumb/Dock_Top.jpg.jpg
