MaterialFoundry/MaterialPlane/Img/Beta Hardware/Guide/.thumb/Pen.jpg.jpg

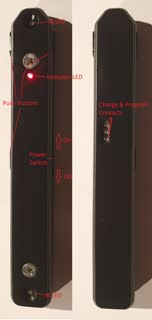
Img/Beta Hardware/Guide/.thumb/Pen.jpg.jpg
