MaterialFoundry/MaterialPlane/Img/Beta Hardware/Guide/.thumb/Pen_CenterSw.jpg.jpg

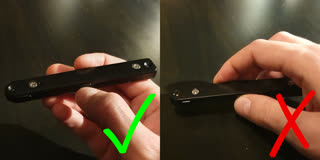
Img/Beta Hardware/Guide/.thumb/Pen_CenterSw.jpg.jpg
