MaterialFoundry/MaterialPlane/Img/Beta Hardware/Guide/.thumb/Pen_ChargePort.jpg.jpg

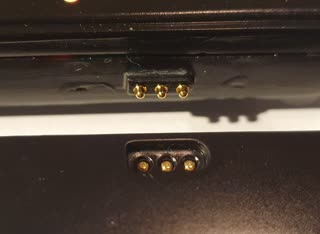
Img/Beta Hardware/Guide/.thumb/Pen_ChargePort.jpg.jpg
