MaterialFoundry/MaterialPlane/Img/Beta Hardware/Guide/.thumb/PenMenu.png.jpg

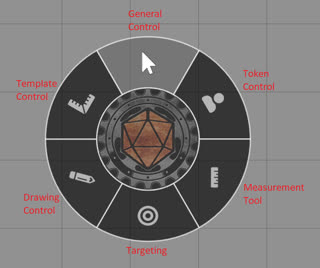
Img/Beta Hardware/Guide/.thumb/PenMenu.png.jpg
