MaterialFoundry/MaterialPlane/Img/Beta Hardware/Guide/.thumb/PenMenu_Drawing.png.jpg

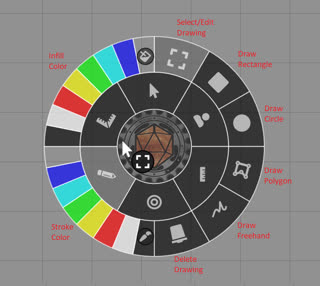
Img/Beta Hardware/Guide/.thumb/PenMenu_Drawing.png.jpg
