MaterialFoundry/MaterialPlane/Img/Beta Hardware/Guide/.thumb/PenMenu_Template.png.jpg

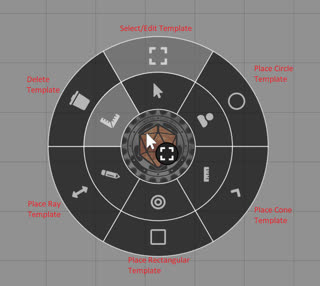
Img/Beta Hardware/Guide/.thumb/PenMenu_Template.png.jpg
