MaterialFoundry/MaterialPlane/Img/Beta Hardware/Guide/.thumb/PenSwitches.jpg.jpg

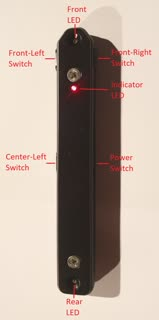
Img/Beta Hardware/Guide/.thumb/PenSwitches.jpg.jpg
