MaterialFoundry/MaterialPlane/Img/Beta Hardware/Guide/.thumb/Sensor MicStand.jpg.jpg

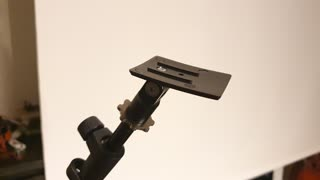
Img/Beta Hardware/Guide/.thumb/Sensor MicStand.jpg.jpg
