MaterialFoundry/MaterialPlane/Img/Beta Hardware/Guide/.thumb/Sensor MicStandMount.jpg.jpg

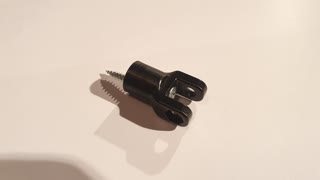
Img/Beta Hardware/Guide/.thumb/Sensor MicStandMount.jpg.jpg
