MaterialFoundry/MaterialPlane/Img/Beta Hardware/Guide/.thumb/Sensor Mounted.jpg.jpg

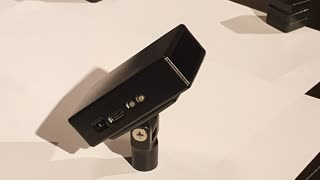
Img/Beta Hardware/Guide/.thumb/Sensor Mounted.jpg.jpg
