MaterialFoundry/MaterialPlane/Img/Beta Hardware/Guide/.thumb/Sensor+Exp2.jpg.jpg

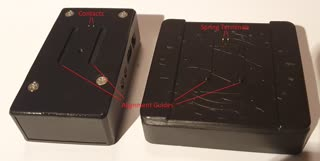
Img/Beta Hardware/Guide/.thumb/Sensor+Exp2.jpg.jpg
