MaterialFoundry/MaterialPlane/Img/Beta Hardware/Guide/.thumb/Sensor+Exp.jpg.jpg

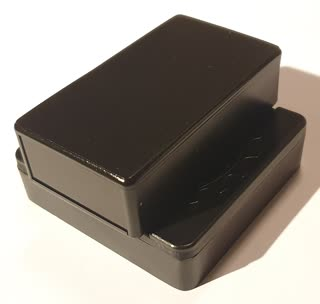
Img/Beta Hardware/Guide/.thumb/Sensor+Exp.jpg.jpg
