MaterialFoundry/MaterialPlane/Img/Beta Hardware/Guide/.thumb/Webserver-Coordinates.jpg.jpg

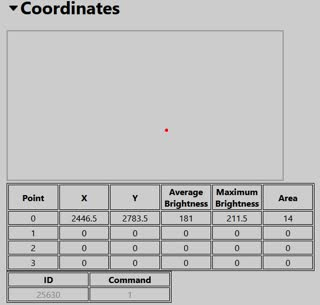
Img/Beta Hardware/Guide/.thumb/Webserver-Coordinates.jpg.jpg
