MaterialFoundry/MaterialPlane/Img/Beta Hardware/Guide/.thumb/Webserver-Status.jpg.jpg

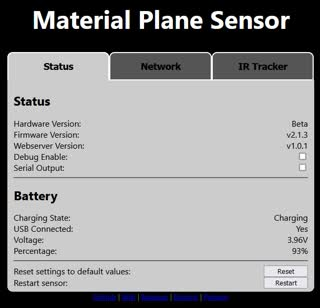
Img/Beta Hardware/Guide/.thumb/Webserver-Status.jpg.jpg
