MaterialFoundry/MaterialPlane/Img/Beta Hardware/Guide/BaseMvmtAngle.jpg

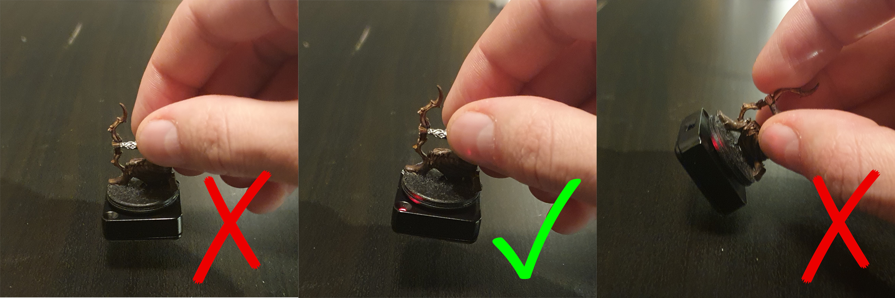
Img/Beta Hardware/Guide/BaseMvmtAngle.jpg
