MaterialFoundry/MaterialPlane/Img/Beta Hardware/Guide/Pen_Bottom.jpg

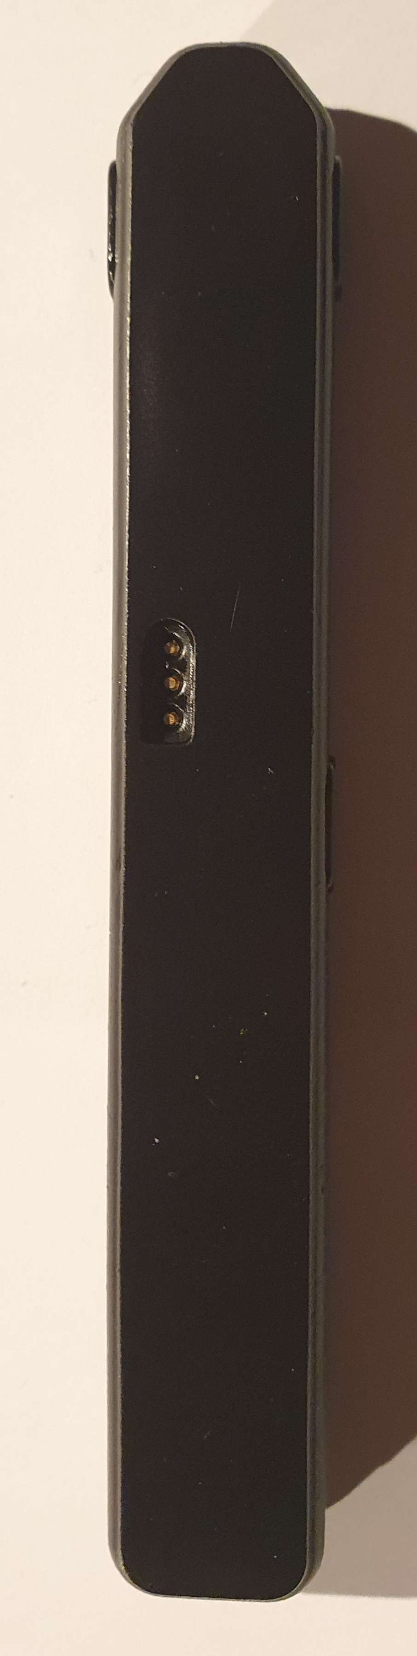
Img/Beta Hardware/Guide/Pen_Bottom.jpg
