MaterialFoundry/MaterialPlane/Img/Beta Hardware/Guide/Pen_Holding.jpg

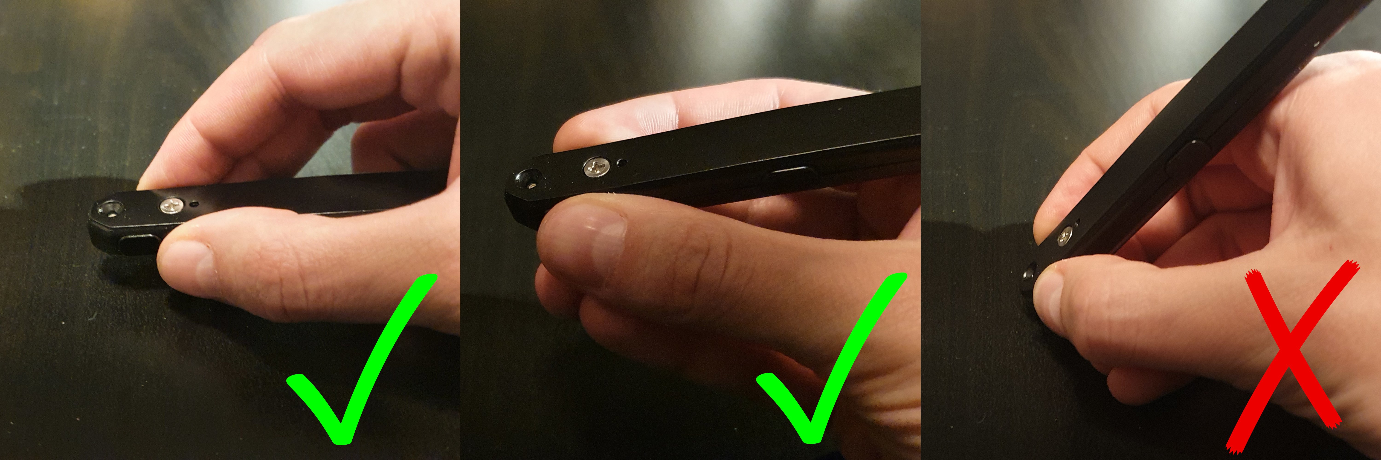
Img/Beta Hardware/Guide/Pen_Holding.jpg
