MaterialFoundry/MaterialPlane/Img/Beta Hardware/Guide/Pen_Top.jpg

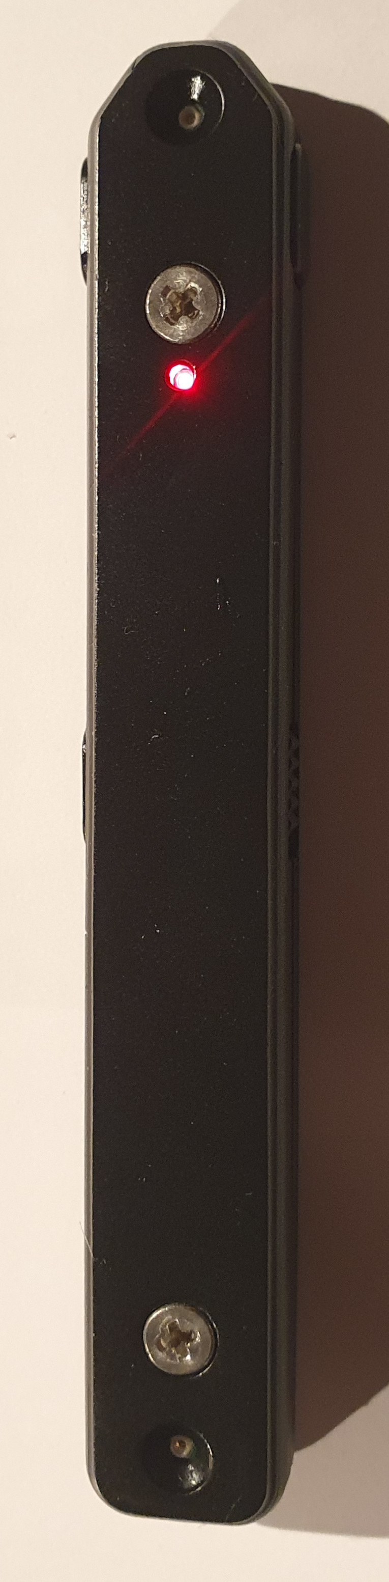
Img/Beta Hardware/Guide/Pen_Top.jpg
