MaterialFoundry/MaterialPlane/Img/Beta Hardware/Guide/PenMenu.png

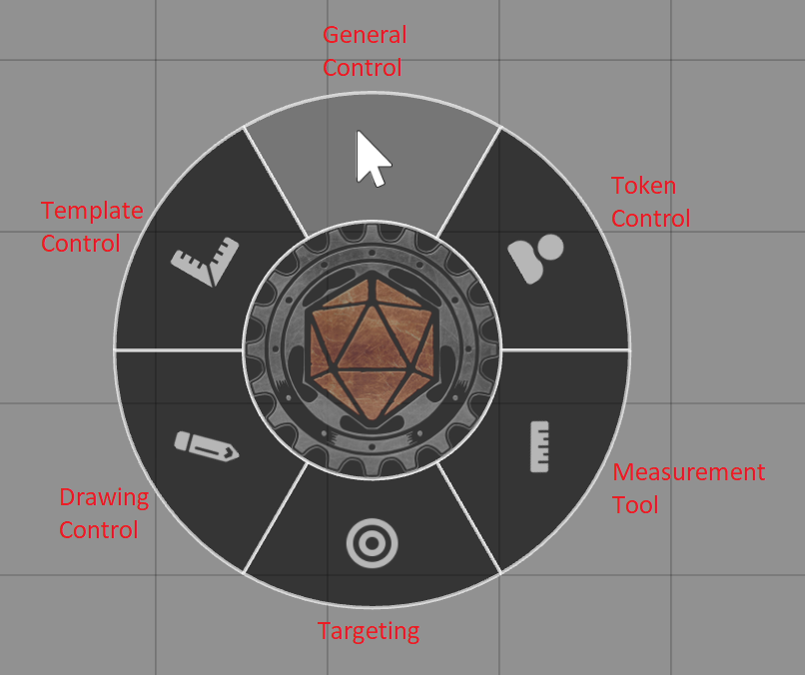
Img/Beta Hardware/Guide/PenMenu.png
