MaterialFoundry/MaterialPlane/Img/Beta Hardware/Guide/Sensor MicStandMount.jpg

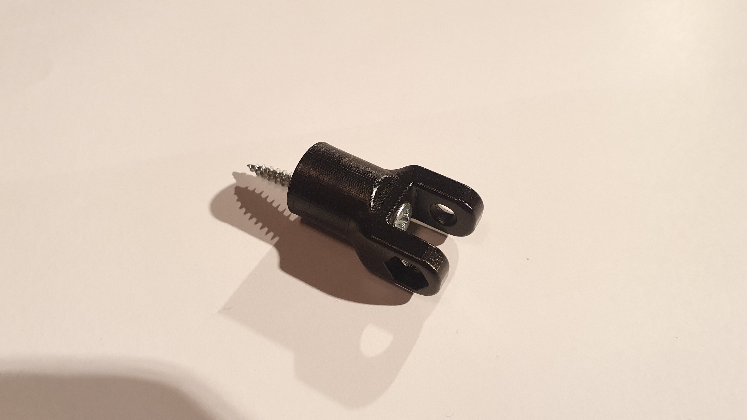
Img/Beta Hardware/Guide/Sensor MicStandMount.jpg
