MaterialFoundry/MaterialPlane/Img/Beta Hardware/Guide/Sensor Mount.jpg

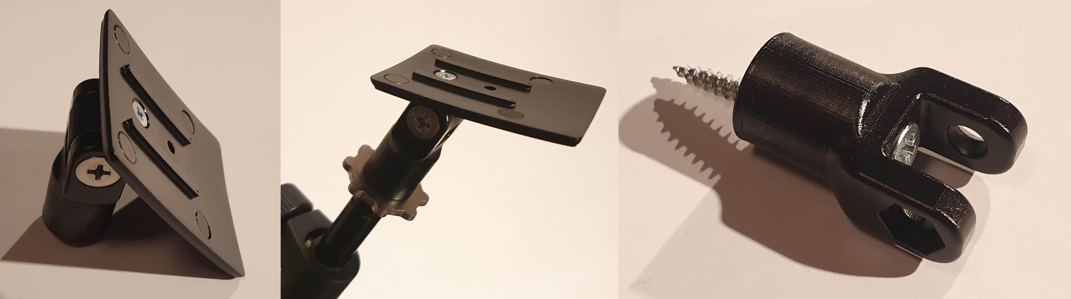
Img/Beta Hardware/Guide/Sensor Mount.jpg
