MaterialFoundry/MaterialPlane/Img/DIY Hardware/.thumb/LEDWiring.jpg.jpg

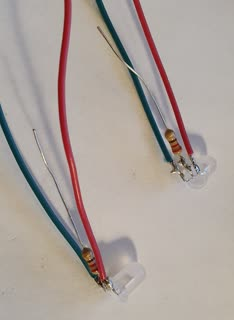
Img/DIY Hardware/.thumb/LEDWiring.jpg.jpg
