MaterialFoundry/MaterialPlane/Img/DIY Hardware/.thumb/SensorWiring.jpg.jpg

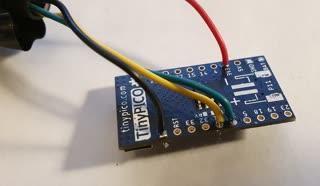
Img/DIY Hardware/.thumb/SensorWiring.jpg.jpg
