MaterialFoundry/MaterialPlane/Img/Module/.thumb/BaseSetup.png.jpg

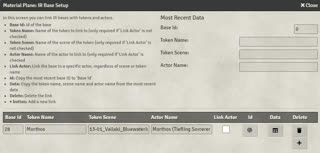
Img/Module/.thumb/BaseSetup.png.jpg
