MaterialFoundry/MaterialPlane/Img/Module/.thumb/BaseSetupButton.png.jpg

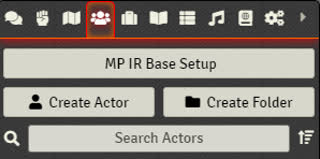
Img/Module/.thumb/BaseSetupButton.png.jpg
