MaterialFoundry/MaterialPlane/Img/Module/.thumb/RemoteSetup.png.jpg

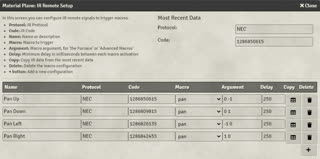
Img/Module/.thumb/RemoteSetup.png.jpg
