MaterialFoundry/MaterialPlane/Img/Module/BaseSetupButton.png

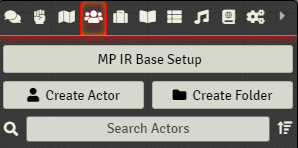
Img/Module/BaseSetupButton.png
