MaterialFoundry/MaterialPlane/Img/Module/RemoteSetup.png

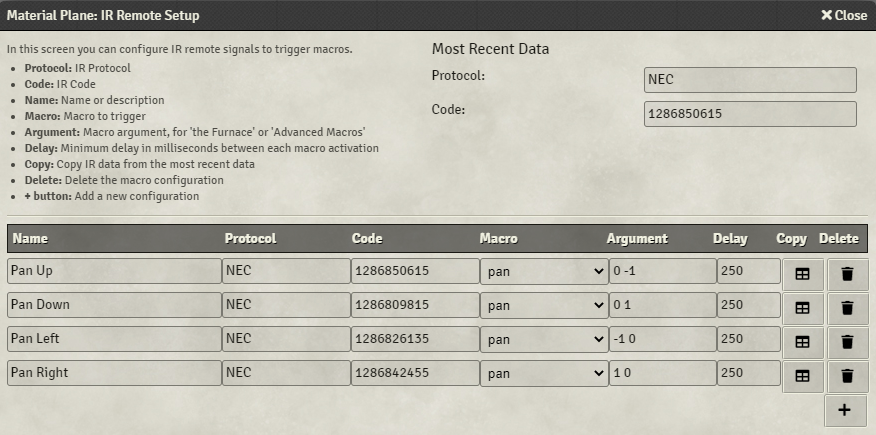
Img/Module/RemoteSetup.png
