MaterialFoundry/MaterialPlane/Img/Other/SensorSetup.jpg

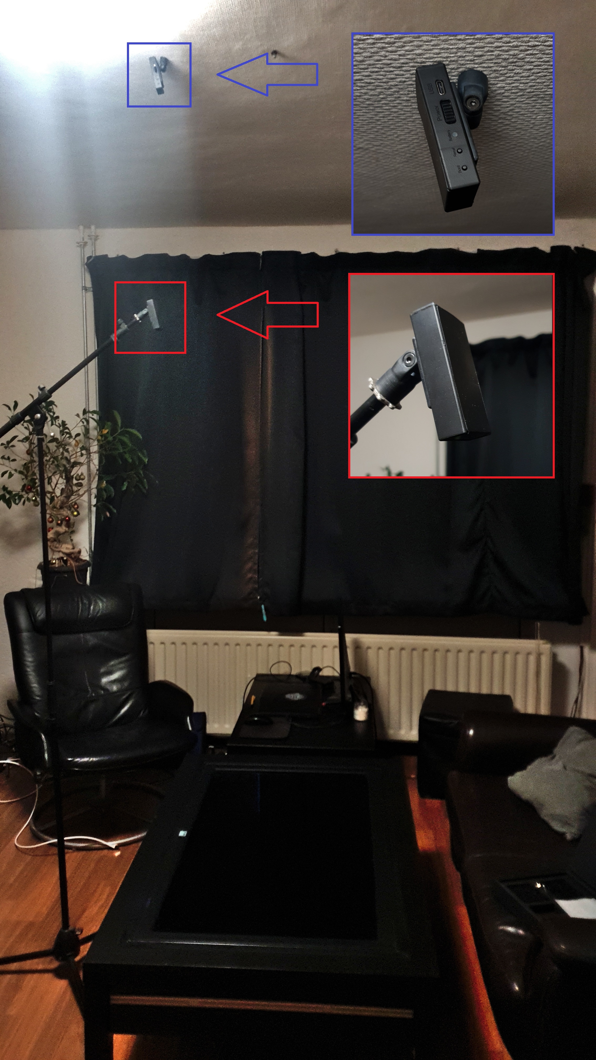
Img/Other/SensorSetup.jpg
