MaterialFoundry/MaterialPlane/docs/img/misc/.thumb/Calibration_Base_Pos.png.jpg

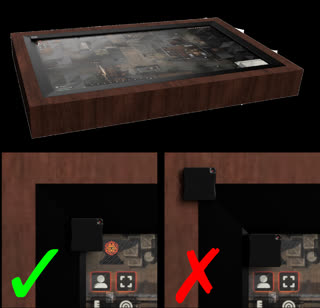
docs/img/misc/.thumb/Calibration_Base_Pos.png.jpg
