MaterialFoundry/MaterialPlane/docs/img/misc/.thumb/Calibration_Multi.png.jpg

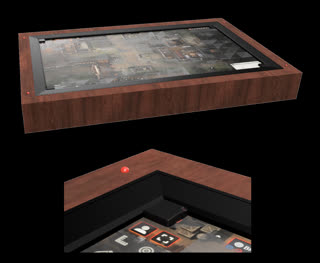
docs/img/misc/.thumb/Calibration_Multi.png.jpg
