MaterialFoundry/MaterialPlane/docs/img/misc/Calibration_Base_Pos.png

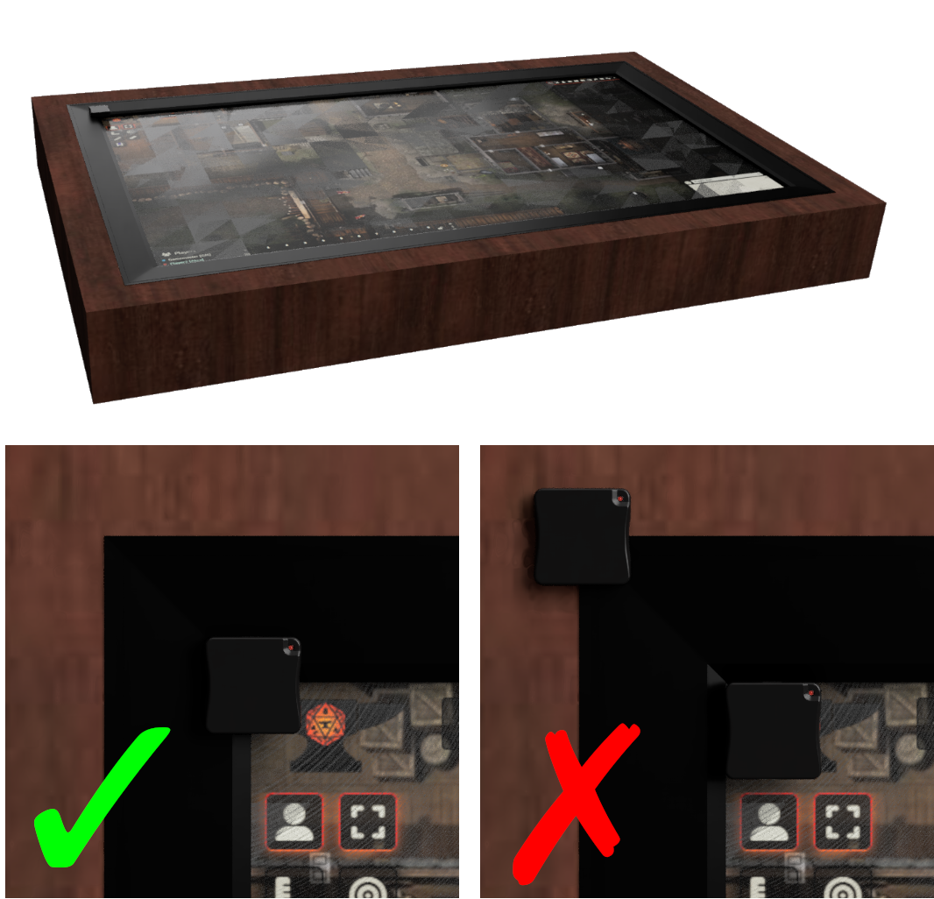
docs/img/misc/Calibration_Base_Pos.png
