MaterialFoundry/MaterialPlane/docs/img/misc/Calibration_Multi.png

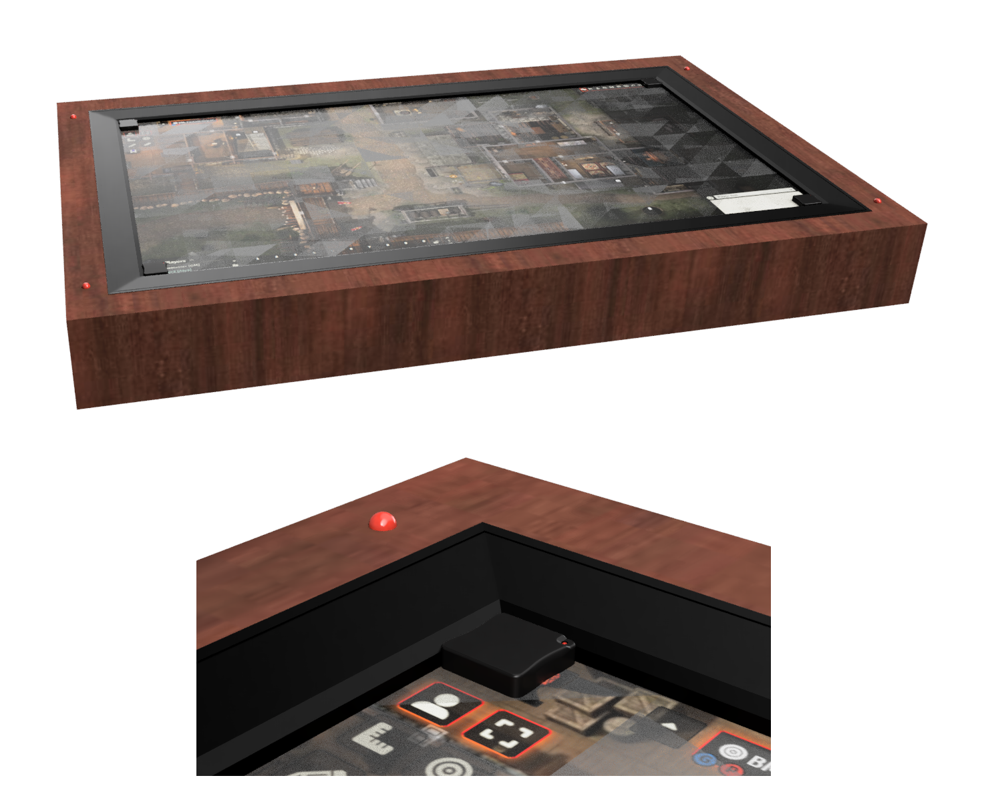
docs/img/misc/Calibration_Multi.png
