MaterialFoundry/MaterialPlane/Img/Module/.thumb/CalibrationButton.png.jpg

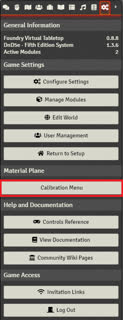
Img/Module/.thumb/CalibrationButton.png.jpg
