MaterialFoundry/MaterialPlane/Img/Module/.thumb/CalibrationMenu.png.jpg

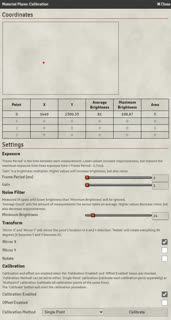
Img/Module/.thumb/CalibrationMenu.png.jpg
