MaterialFoundry/MaterialPlane/Img/Module/.thumb/CalibrationProcess.jpg.jpg

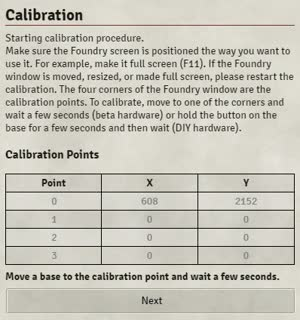
Img/Module/.thumb/CalibrationProcess.jpg.jpg
