MaterialFoundry/MaterialPlane/Img/Module/.thumb/CalibrationProcess.png.jpg

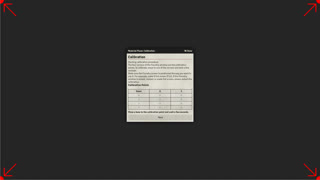
Img/Module/.thumb/CalibrationProcess.png.jpg
